mikepimez/FdD_Equipo_13/Fund Diseño/Talleres/Taller_10/Onshape Modelado 3D/README.md

# ONSHAPE Modelado 3D
## Link Ecovent:
## https://cad.onshape.com/documents/2ff0832ba7d75a162150be3a/w/7356b8713903647c55373f1b/e/d87a3bc96895a205dabae675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
