mikepimez/FdD_Equipo_13/Fund Diseño/Talleres/Taller_7/Certificados Onshape/Elmer David Bravo Tumbay/Introduction to onshape-Elmer David Bravo Tumbay.pdf

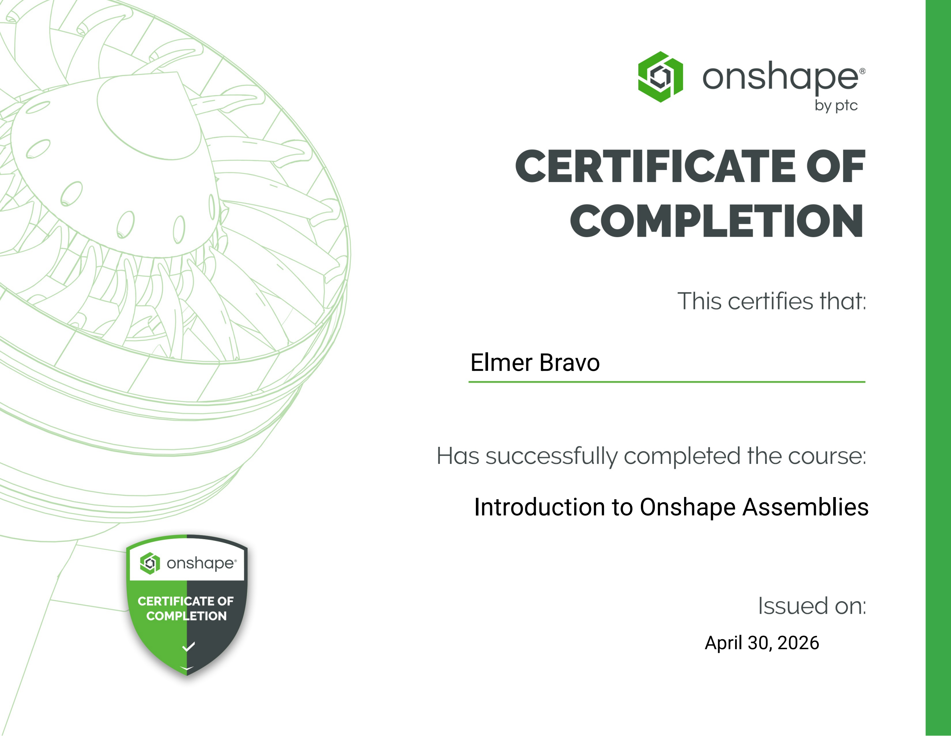
[picture p20: page 1]

Elmer Bravo

April 30, 2026

Introduction to Onshape Assemblies
