mikepimez/FdD_Equipo_13/Fund Diseño/Talleres/Taller_7/Certificados Onshape/Aldair Silvera Huaman/aldair-silvera-huaman-80f540d1-5e13-4ac5-9597-b1e16f2ed07b-certificate.pdf

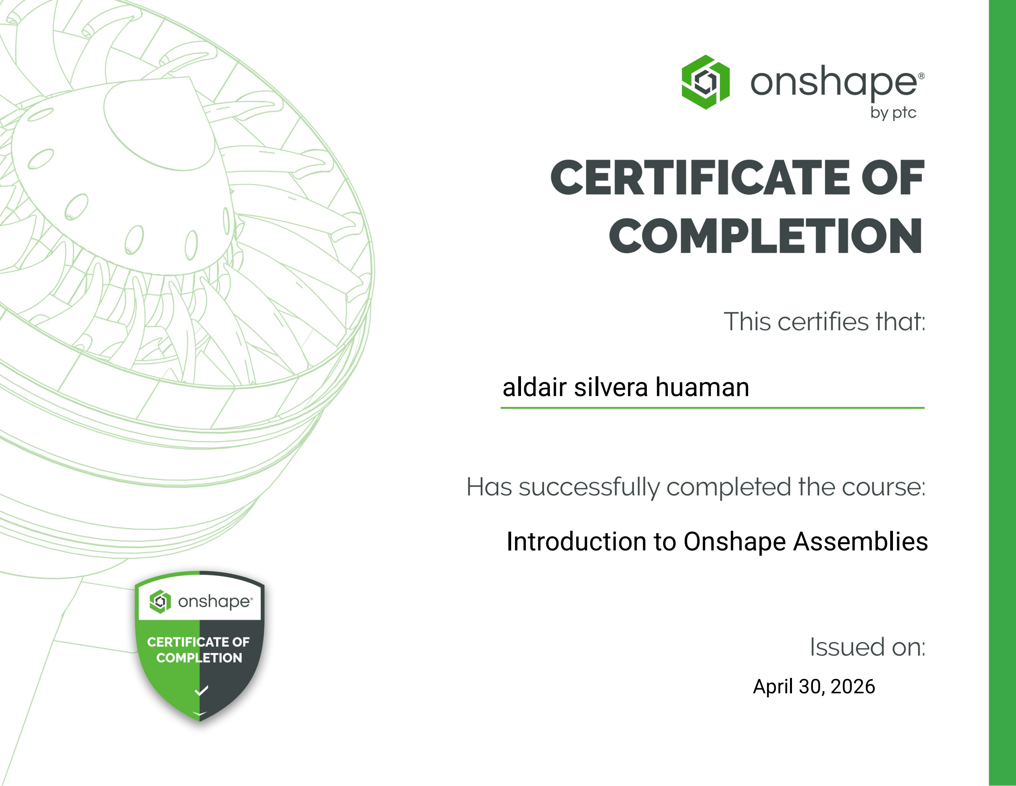
[picture p21: page 1]

aldair silvera huaman

April 30, 2026

Introduction to Onshape Assemblies
