mikepimez/FdD_Equipo_13/Fund Diseño/Talleres/Taller_7/Certificados Onshape/Milagros Lucero Romero Yllaconza/milagros-romero-127f4364-2a7c-48cf-9cd8-1c9b132f20d1-certificate.pdf

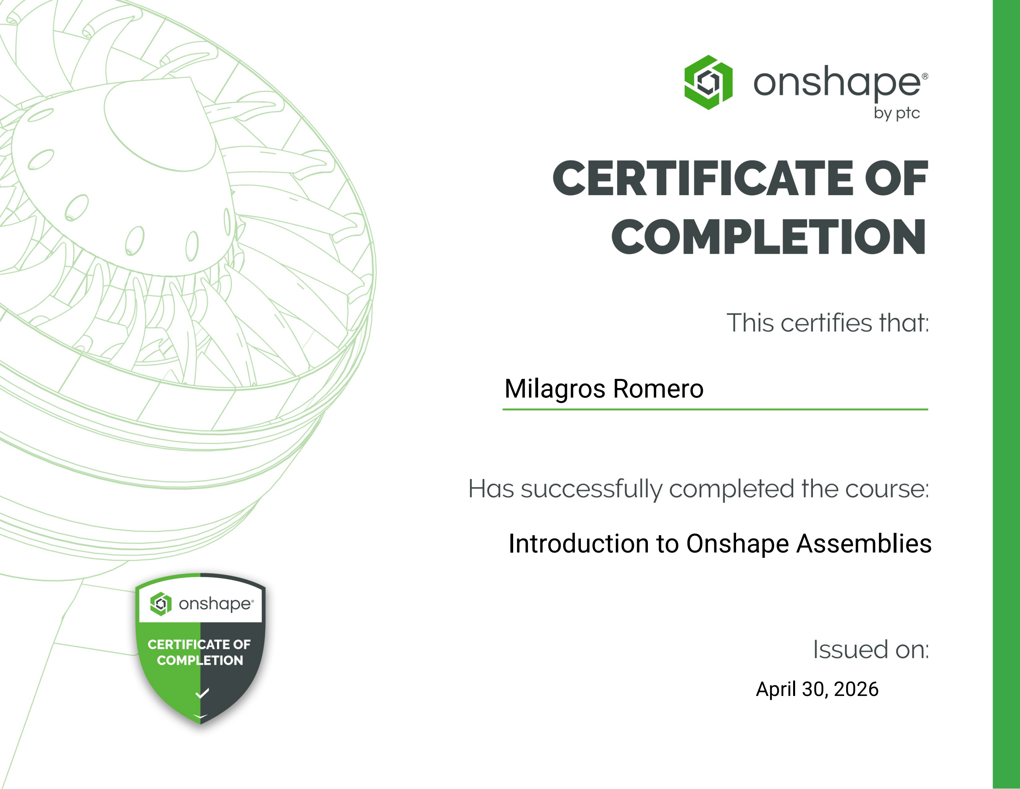
[picture p22: page 1]

Milagros Romero

April 30, 2026

Introduction to Onshape Assemblies
