mikepimez/FdD_Equipo_13/Proyecto/MóduloMecánico/Certificados/Milagros Romero Yllaconza/CertificadosUnidos.pdf

Milagros Romero

Introduction to Sketching

April 30, 2026

Milagros Romero

Introduction to Part Studios

April 30, 2026

Milagros Romero

April 30, 2026

Introduction to Onshape Assemblies

Milagros Romero

April 30, 2026

Detailed Drawings

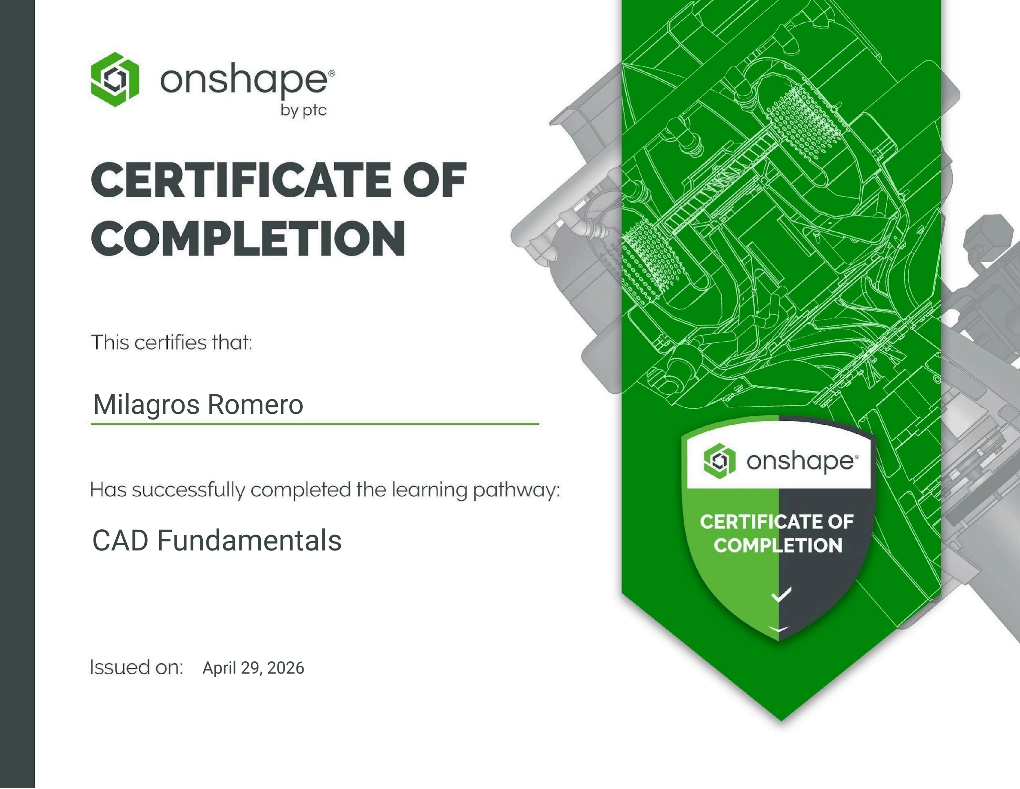
[picture p23: page 5]

Milagros Romero

CAD Fundamentals

April 29, 2026
