mikepimez/FdD_Equipo_13/Proyecto/MóduloMecánico/Certificados/Isabel Padilla Romero/CertificadosUnidos.pdf

Isabel Antonella Padilla Romero

Introduction to Sketching

April 30, 2026

Isabel Antonella Padilla Romero

Introduction to Part Studios

April 30, 2026

Isabel Antonella Padilla Romero

Introduction to Onshape Assemblies

April 30, 2026

Isabel Antonella Padilla Romero

Detailed Drawings

April 30, 2026

Isabel Antonella Padilla Romero

CAD Fundamentals

April 29, 2026
