mikepimez/FdD_Equipo_13/Proyecto/MóduloMecánico/Certificados/David Bravo Tumbay/CertificadosUnidos.pdf

Elmer Bravo

Introduction to Sketching

April 30, 2026

Elmer Bravo

Introduction to Part Studios

April 30, 2026

Elmer Bravo

April 30, 2026

Introduction to Onshape Assemblies

Elmer Bravo

April 30, 2026

Detailed Drawings

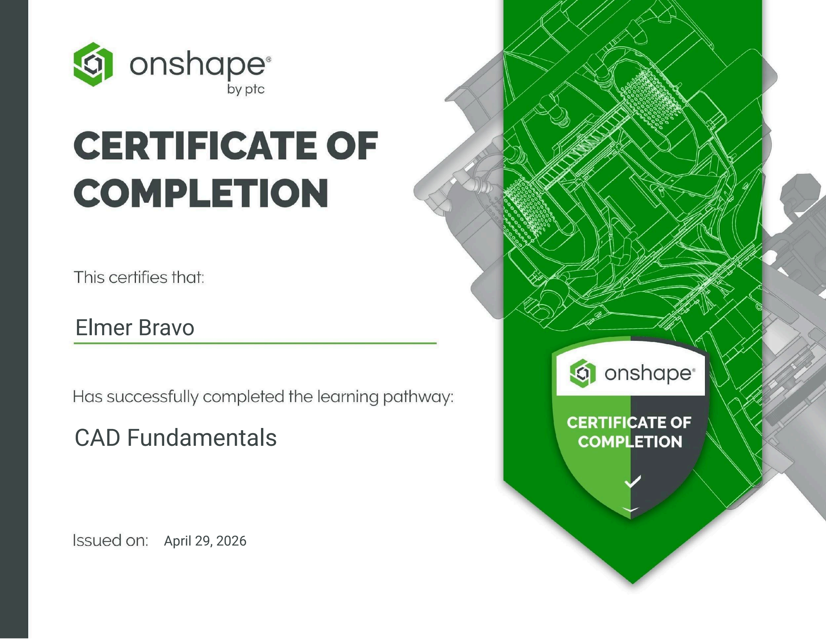
[picture p24: page 5]

Elmer Bravo

CAD Fundamentals

April 29, 2026
