mikepimez/FdD_Equipo_13/Proyecto/MóduloMecánico/Certificados/Aldair Silvera Huaman/CertificadosUnidos.pdf

aldair silvera huaman

Introduction to Sketching

April 30, 2026

aldair silvera huaman

Introduction to Part Studios

April 30, 2026

aldair silvera huaman

April 30, 2026

Introduction to Onshape Assemblies

aldair silvera huaman

April 30, 2026

Detailed Drawings

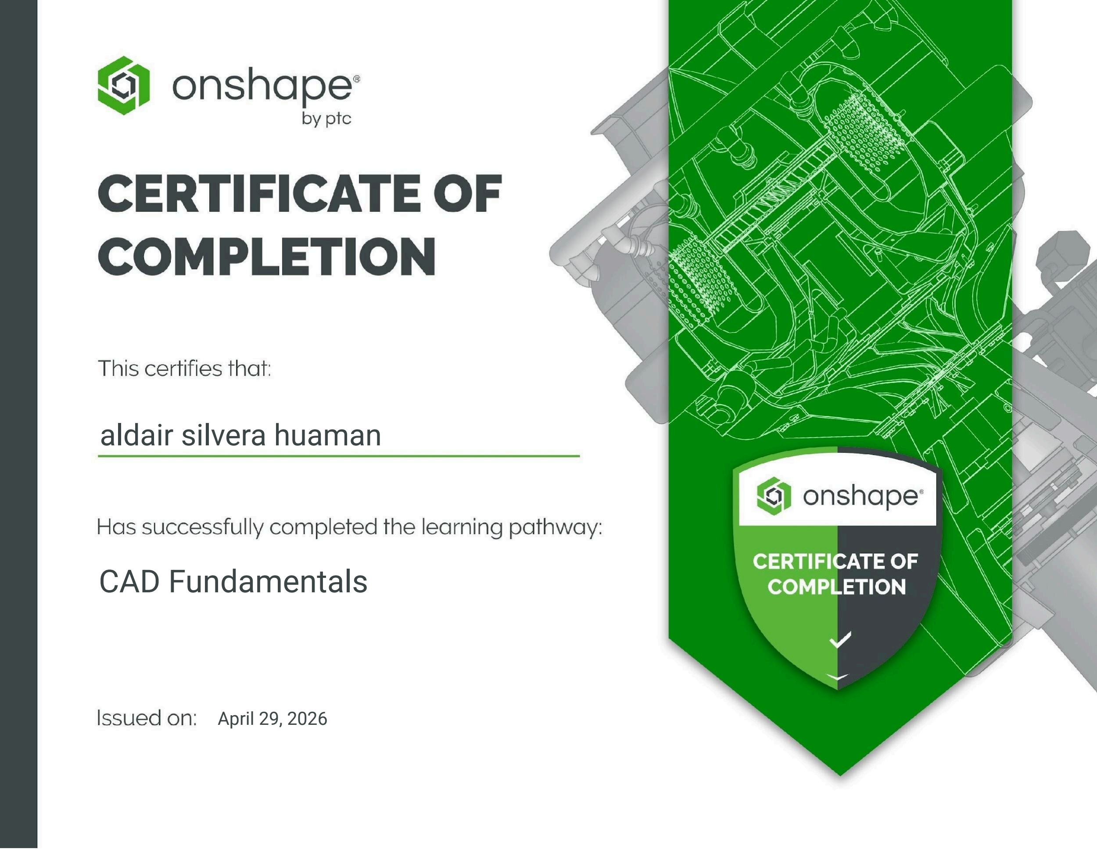
[picture p25: page 5]

aldair silvera huaman

CAD Fundamentals

April 29, 2026
