mikepimez/FdD_Equipo_13/Proyecto/MóduloMecánico/Certificados/Minoru Tapia Gómez/CertificadosUnidos.pdf

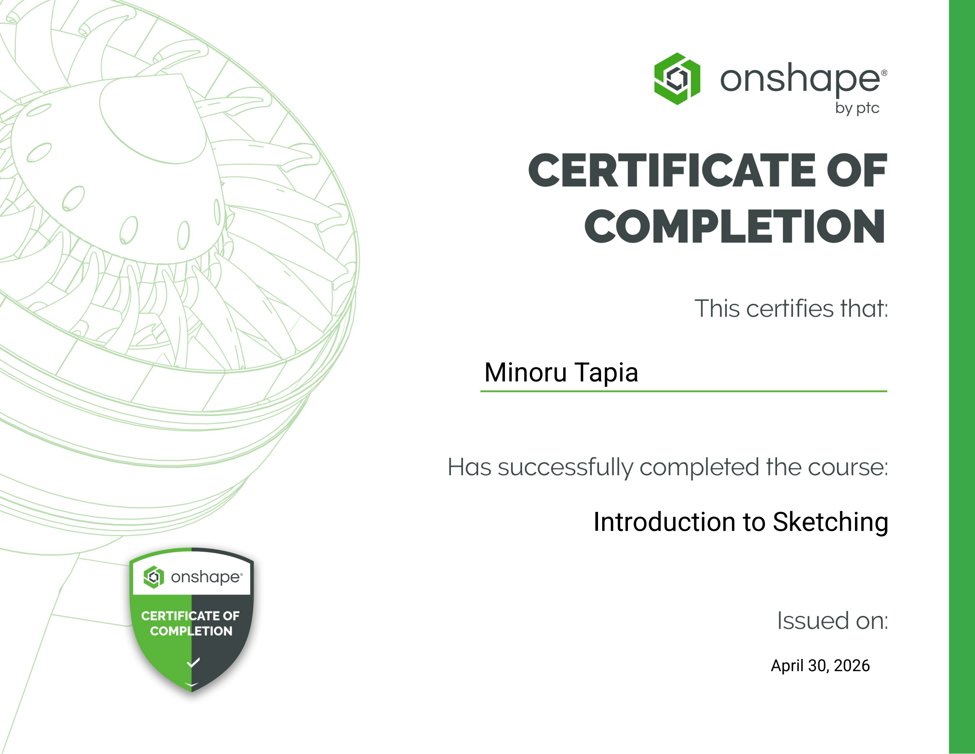
[picture p26: page 1]

## Minoru Tapia

## Introduction to Sketching

April 30, 2026

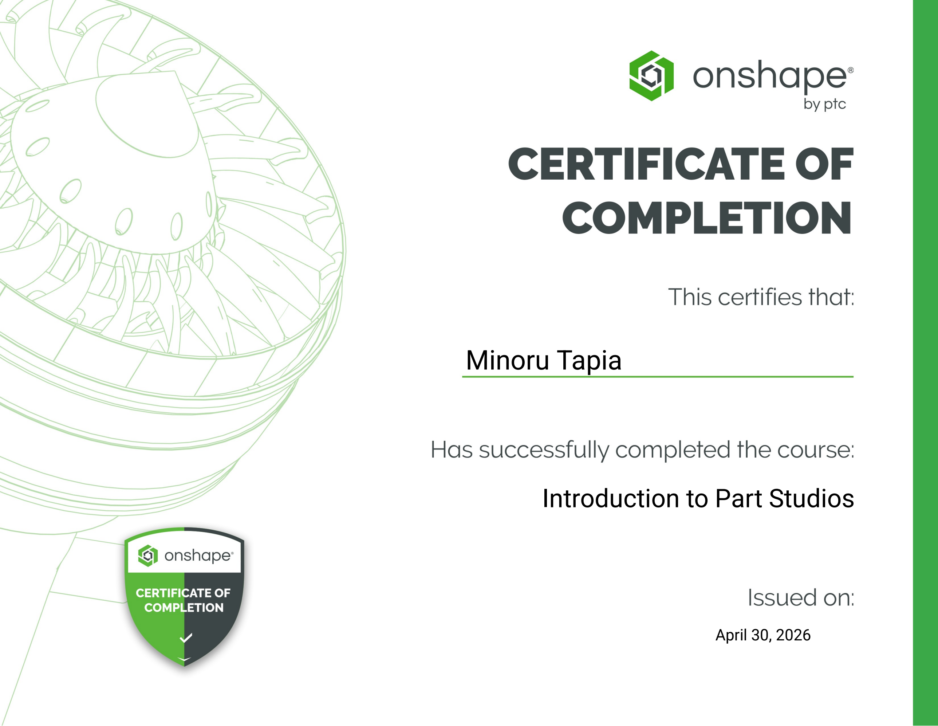
[picture p27: page 2]

## Minoru Tapia

## Introduction to Part Studios

April 30, 2026

Minoru Takeshi Tapia Gomez

Introduction to Onshape Assemblies

April 30, 2026

Minoru Takeshi Tapia Gomez

Detailed Drawings

April 30, 2026

Minoru Tapia

CAD Fundamentals

April 29, 2026
