mikepimez/FdD_Equipo_13/Fund Diseño/Talleres/Taller_7/Certificados Onshape/Elmer David Bravo Tumbay/Detaile Drawings-Elmer David Bravo Tumbay.pdf

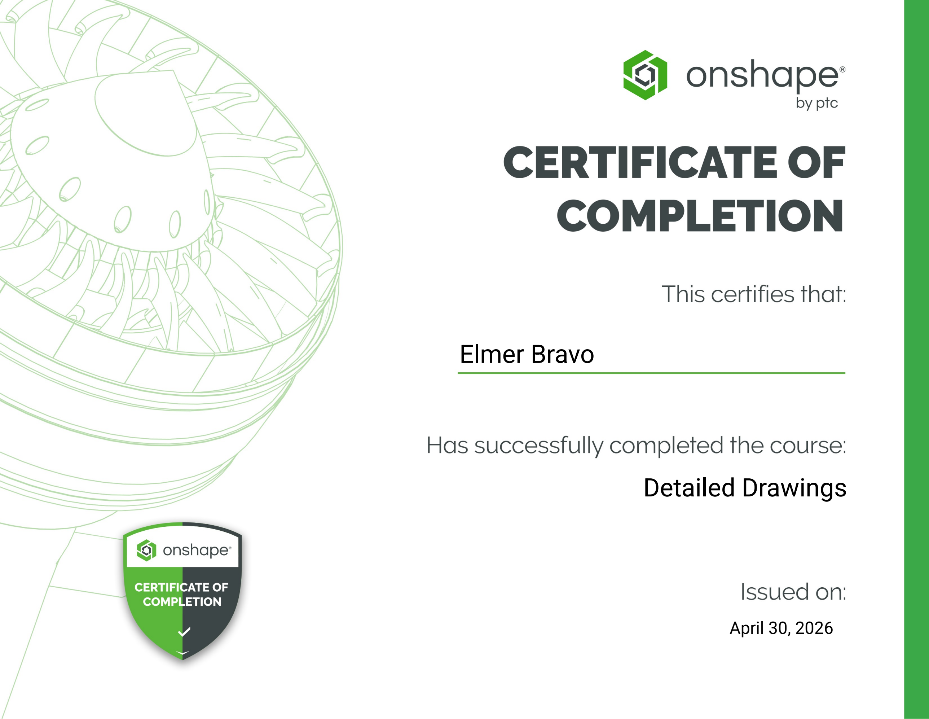
[picture p32: page 1]

Elmer Bravo

April 30, 2026

Detailed Drawings
