mikepimez/FdD_Equipo_13/Fund Diseño/Talleres/Taller_7/Certificados Onshape/Elmer David Bravo Tumbay/Introduction to part studios-Elmer David Bravo Tumbay.pdf

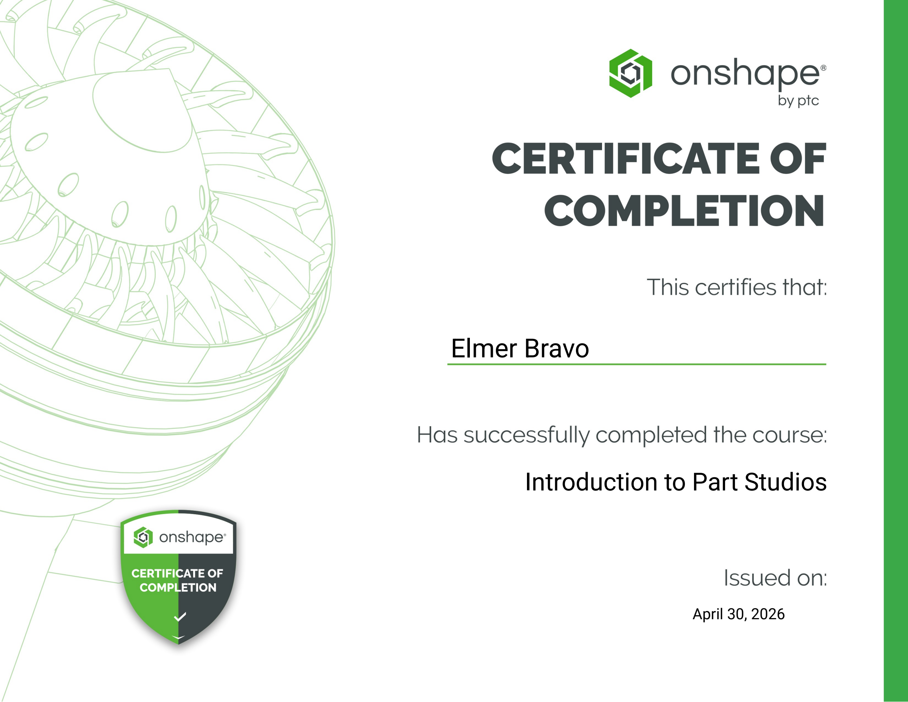
[picture p33: page 1]

Elmer Bravo

Introduction to Part Studios

April 30, 2026
