mikepimez/FdD_Equipo_13/Fund Diseño/Talleres/Taller_7/Certificados Onshape/Elmer David Bravo Tumbay/Introduction to sketching- Bravo Tumbay Elmer David.pdf

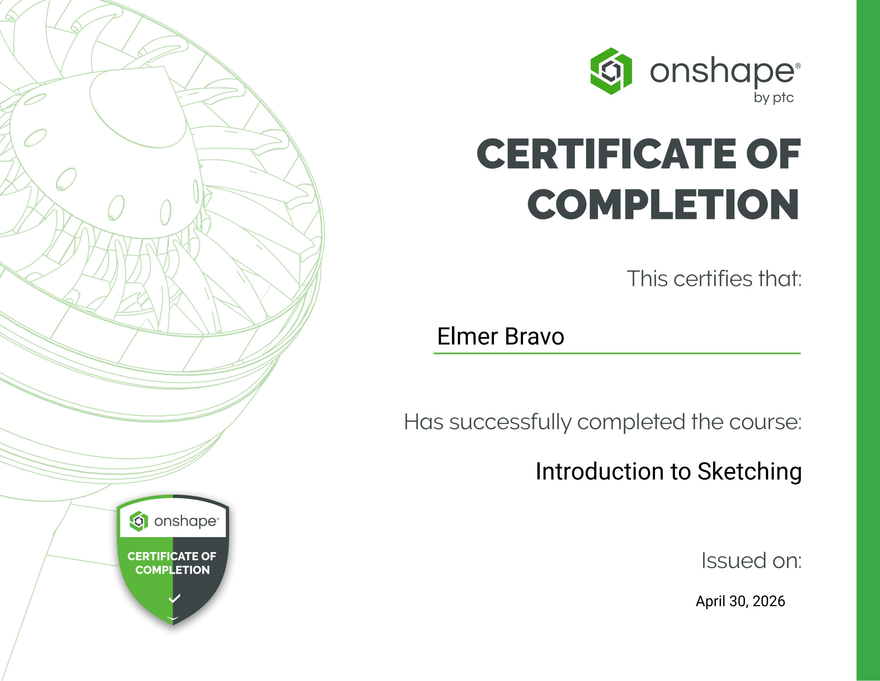
[picture p34: page 1]

Elmer Bravo

Introduction to Sketching

April 30, 2026
