mikepimez/FdD_Equipo_13/Fund Diseño/Talleres/Taller_7/Certificados Onshape/Aldair Silvera Huaman/aldair-silvera-huaman-4e8c6b65-7295-4350-af0d-eef3ffecdfa4-certificate.pdf

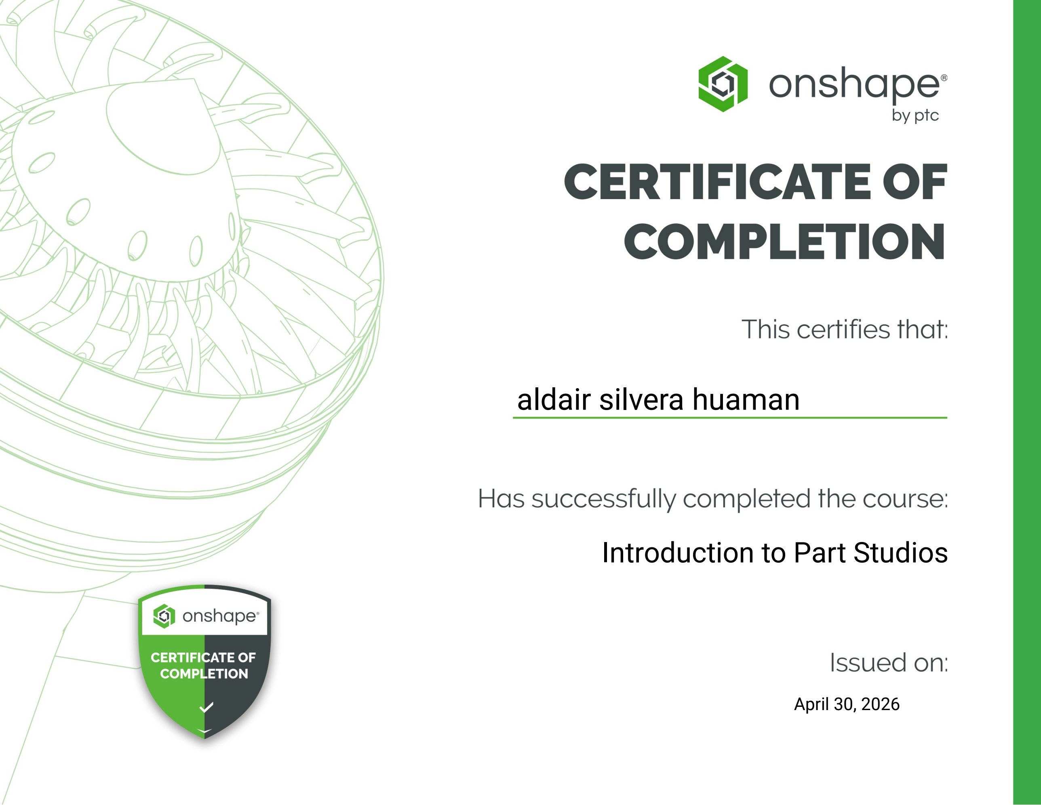
[picture p35: page 1]

aldair silvera huaman

Introduction to Part Studios

April 30, 2026
