mikepimez/FdD_Equipo_13/Fund Diseño/Talleres/Taller_7/Certificados Onshape/Aldair Silvera Huaman/aldair-silvera-huaman-e3dbeebc-8bc2-4efb-8675-0c4b83620323-certificate.pdf

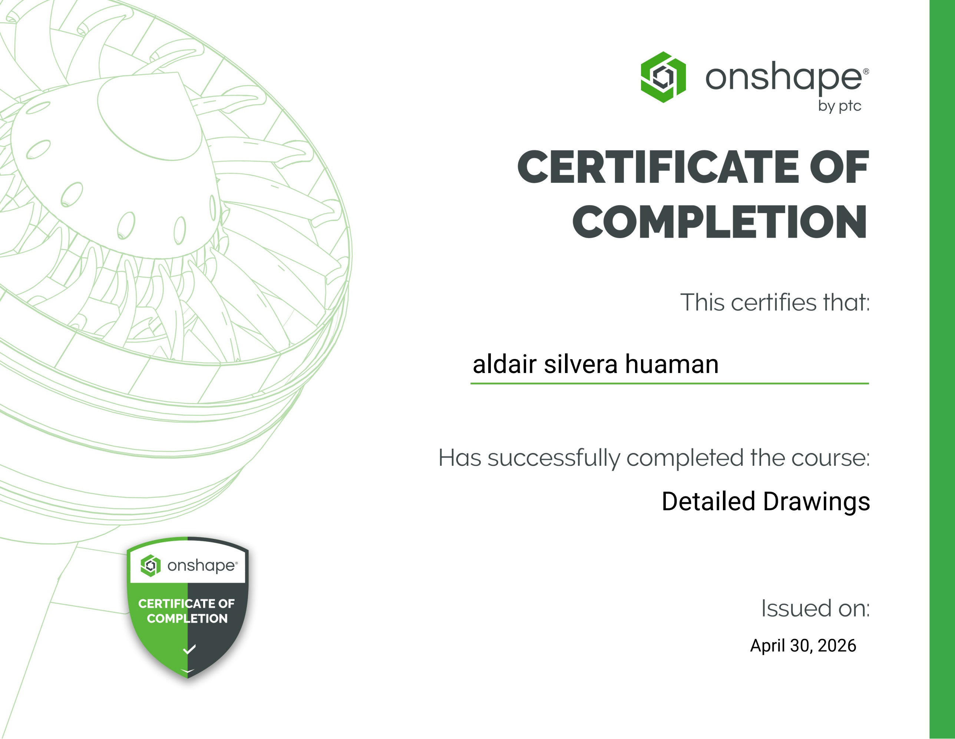
[picture p36: page 1]

aldair silvera huaman

April 30, 2026

Detailed Drawings
