mikepimez/FdD_Equipo_13/Fund Diseño/Talleres/Taller_7/Certificados Onshape/Aldair Silvera Huaman/aldair-silvera-huaman-eca4b5cf-689d-40fd-96bf-5592a26e97f9-certificate.pdf

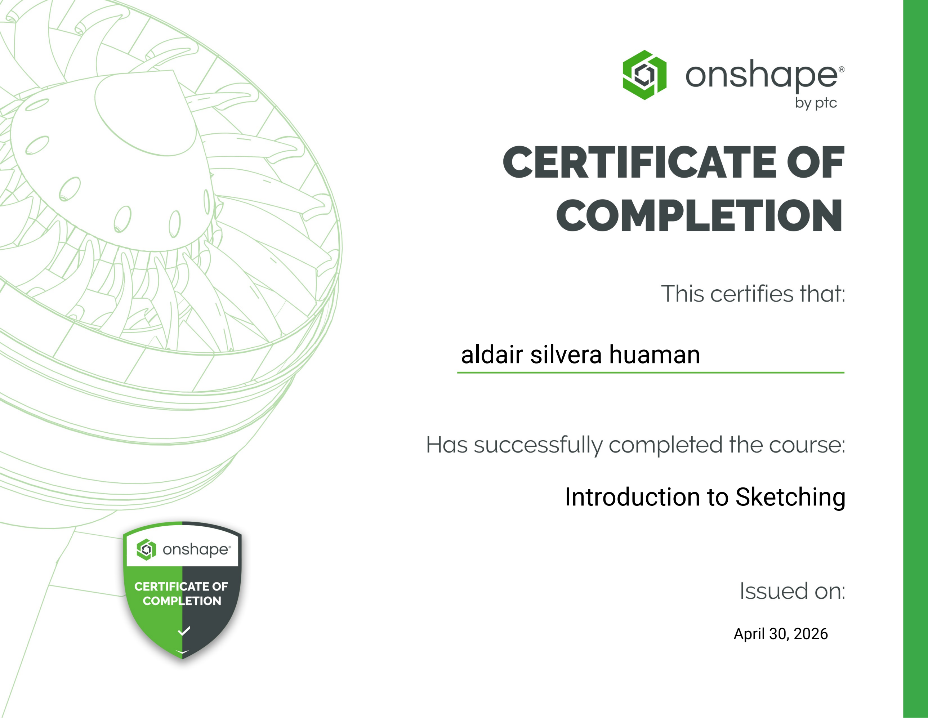
[picture p37: page 1]

aldair silvera huaman

Introduction to Sketching

April 30, 2026
