mikepimez/FdD_Equipo_13/Fund Diseño/Talleres/Taller_7/Certificados Onshape/Milagros Lucero Romero Yllaconza/milagros-romero-22843f85-eb03-4271-b142-8c62b271767d-certificate.pdf

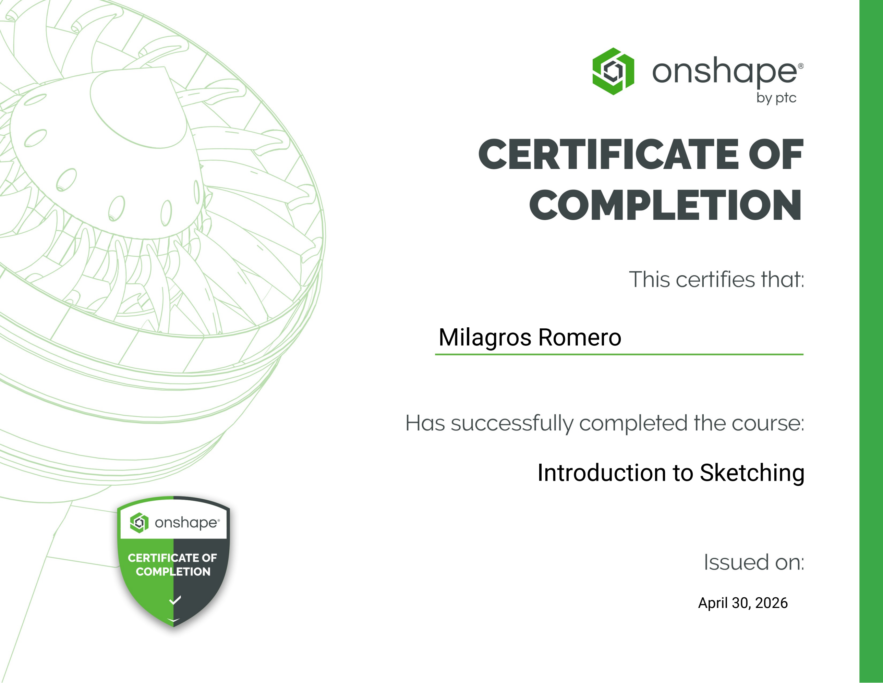
[picture p38: page 1]

Milagros Romero

Introduction to Sketching

April 30, 2026
