mikepimez/FdD_Equipo_13/Fund Diseño/Talleres/Taller_7/Certificados Onshape/Milagros Lucero Romero Yllaconza/milagros-romero-844ef38e-39e2-414a-8ad2-bcf23b460bee-certificate.pdf

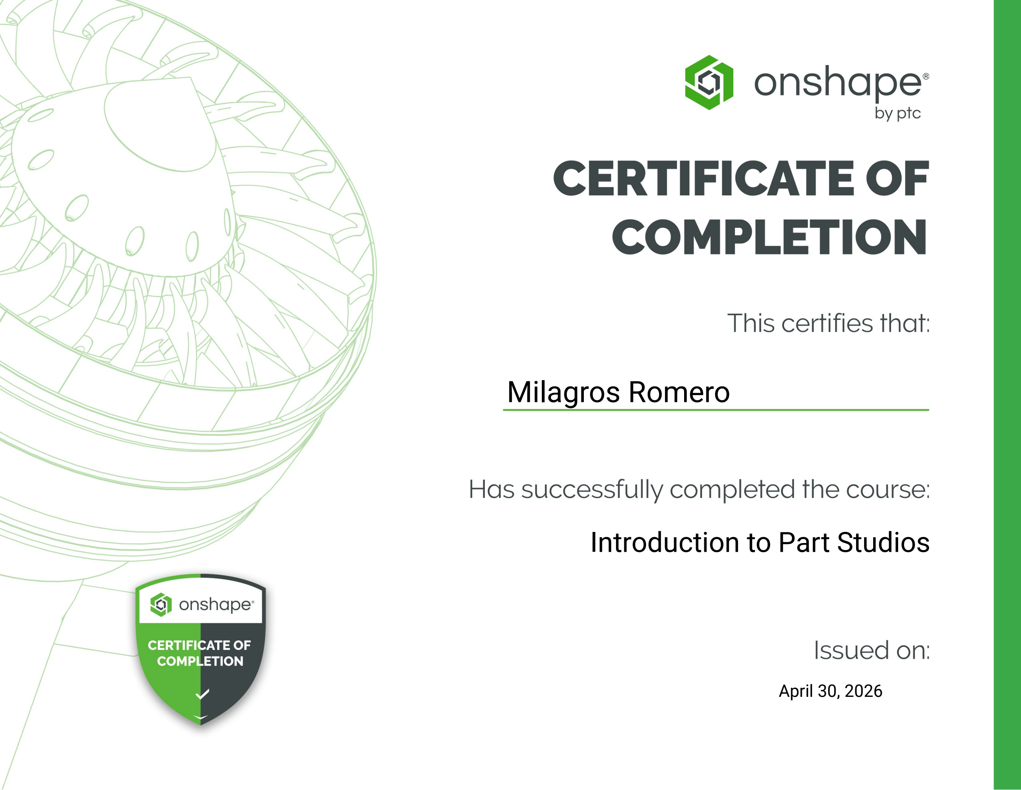
[picture p39: page 1]

Milagros Romero

Introduction to Part Studios

April 30, 2026
