mikepimez/FdD_Equipo_13/Fund Diseño/Talleres/Taller_7/Certificados Onshape/Milagros Lucero Romero Yllaconza/milagros-romero-93da2aa8-beca-4e25-bb0d-afc975d9d456-certificate.pdf

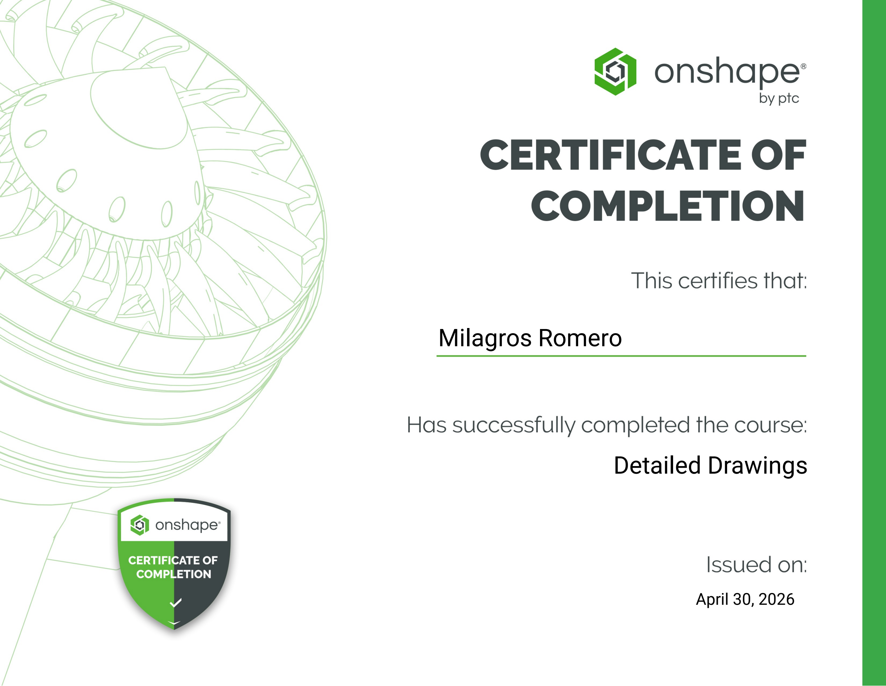
[picture p40: page 1]

Milagros Romero

April 30, 2026

Detailed Drawings
