mikepimez/FdD_Equipo_13/Fund Diseño/Talleres/Taller_7/Certificados Onshape/Isabel Antonella Padilla Romero/Introduction to Part Studios - Isabel Antonella Padilla Romero.pdf

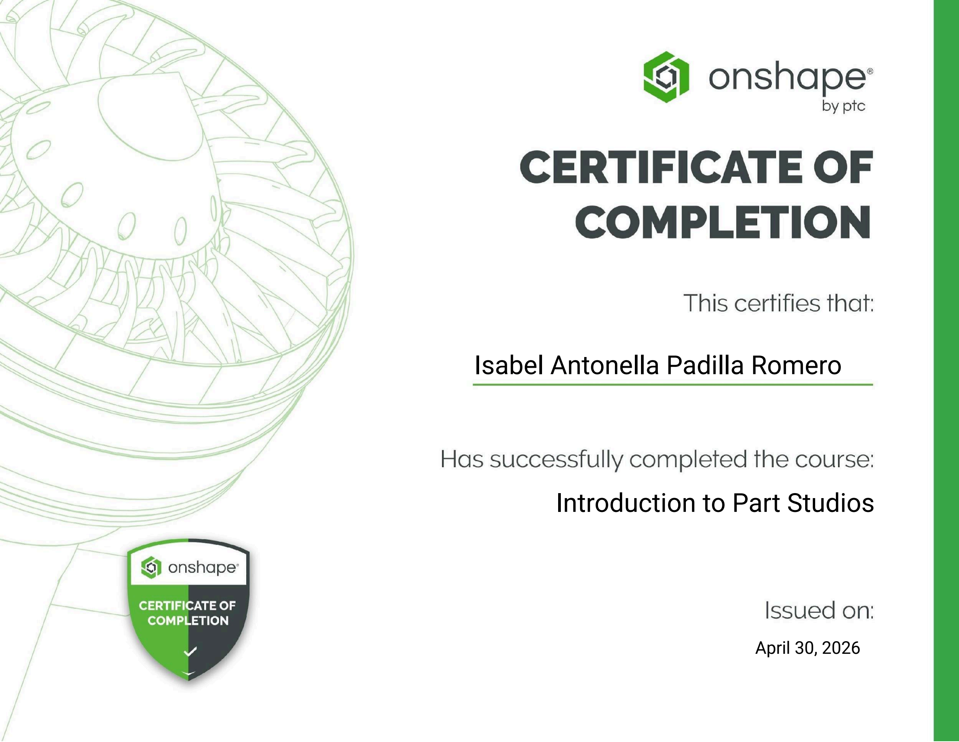
[picture p41: page 1]

Isabel Antonella Padilla Romero

Introduction to Part Studios

April 30, 2026
