mikepimez/FdD_Equipo_13/Fund Diseño/Talleres/Taller_7/Certificados Onshape/Isabel Antonella Padilla Romero/Introduction to Sketching - Isabel Antonella Padilla Romero.pdf

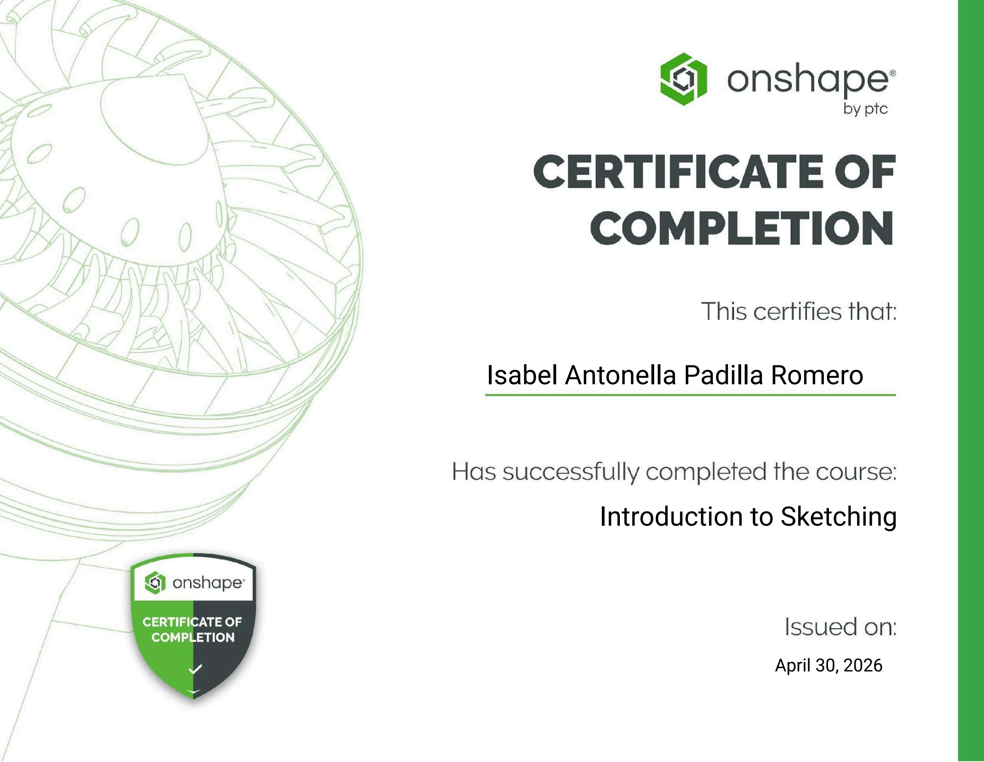
[picture p42: page 1]

Isabel Antonella Padilla Romero

Introduction to Sketching

April 30, 2026
