mikepimez/FdD_Equipo_13/Fund Diseño/Talleres/Taller_7/Certificados Onshape/Minoru Takeshi Tapia Gómez/Introduction to Sketching - Minoru Tapia Gomez.pdf

Minoru Tapia

Introduction to Sketching

April 30, 2026
