mikepimez/FdD_Equipo_13/Fund Diseño/Talleres/Taller_7/Certificados Onshape/Minoru Takeshi Tapia Gómez/Introduction to Part Estudios - Minoru Tapia Gomez.pdf

Minoru Tapia

Introduction to Part Studios

April 30, 2026
