mikepimez/FdD_Equipo_13/Fund Diseño/Talleres/Taller_7/Certificados Onshape/Minoru Takeshi Tapia Gómez/Detailed Drawings - Minoru Takeshi Tapia Gomez.pdf

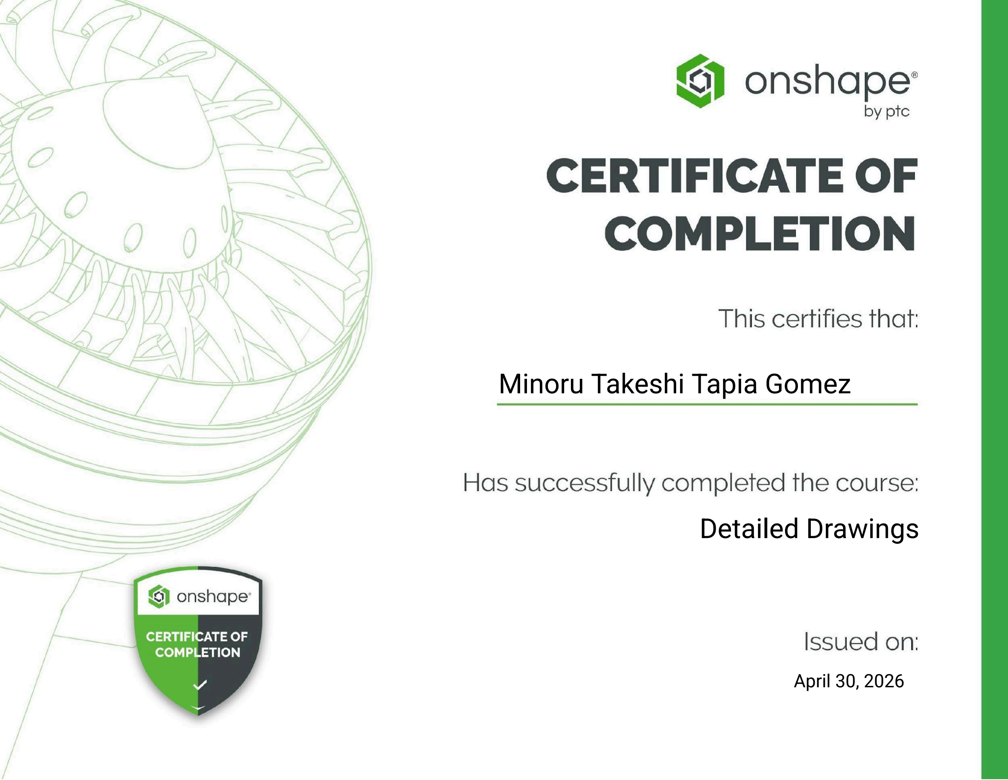
[picture p43: page 1]

Minoru Takeshi Tapia Gomez

Detailed Drawings

April 30, 2026
