mikepimez/FdD_Equipo_13/Fund Diseño/Talleres/Taller_7/Certificados Onshape/Isabel Antonella Padilla Romero/Detailed Drawings - Isabel Antonella Padilla Romero.pdf

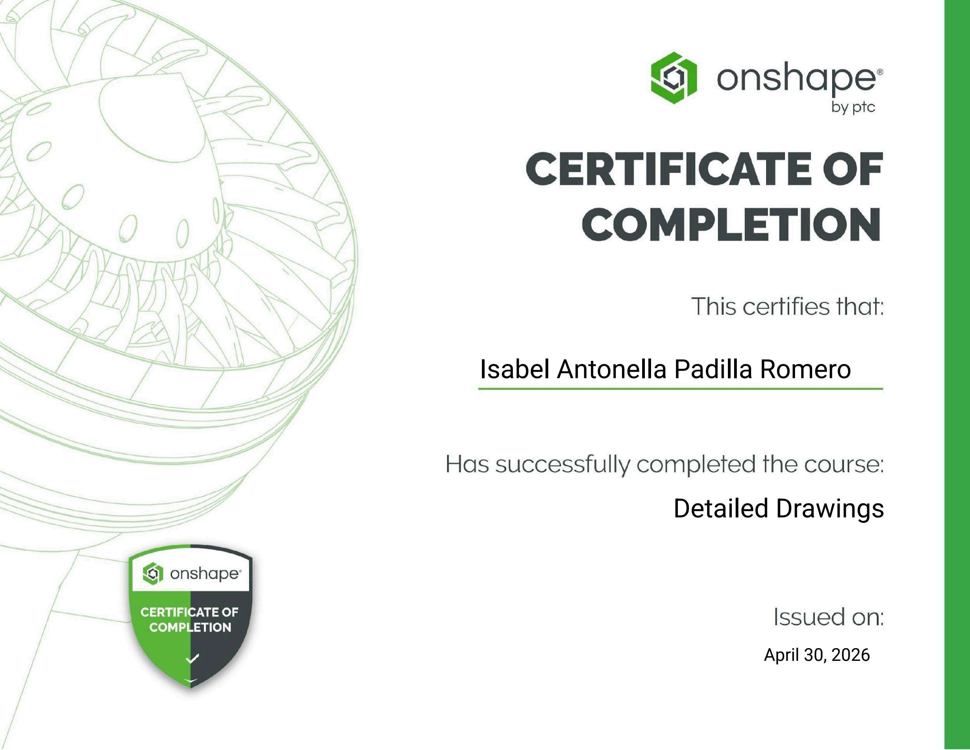
[picture p44: page 1]

Isabel Antonella Padilla Romero

Detailed Drawings

April 30, 2026
