mikepimez/FdD_Equipo_13/Proyecto/MóduloMecánico/VFINAL/Bocetos/Boceto interior VFINAL.pdf

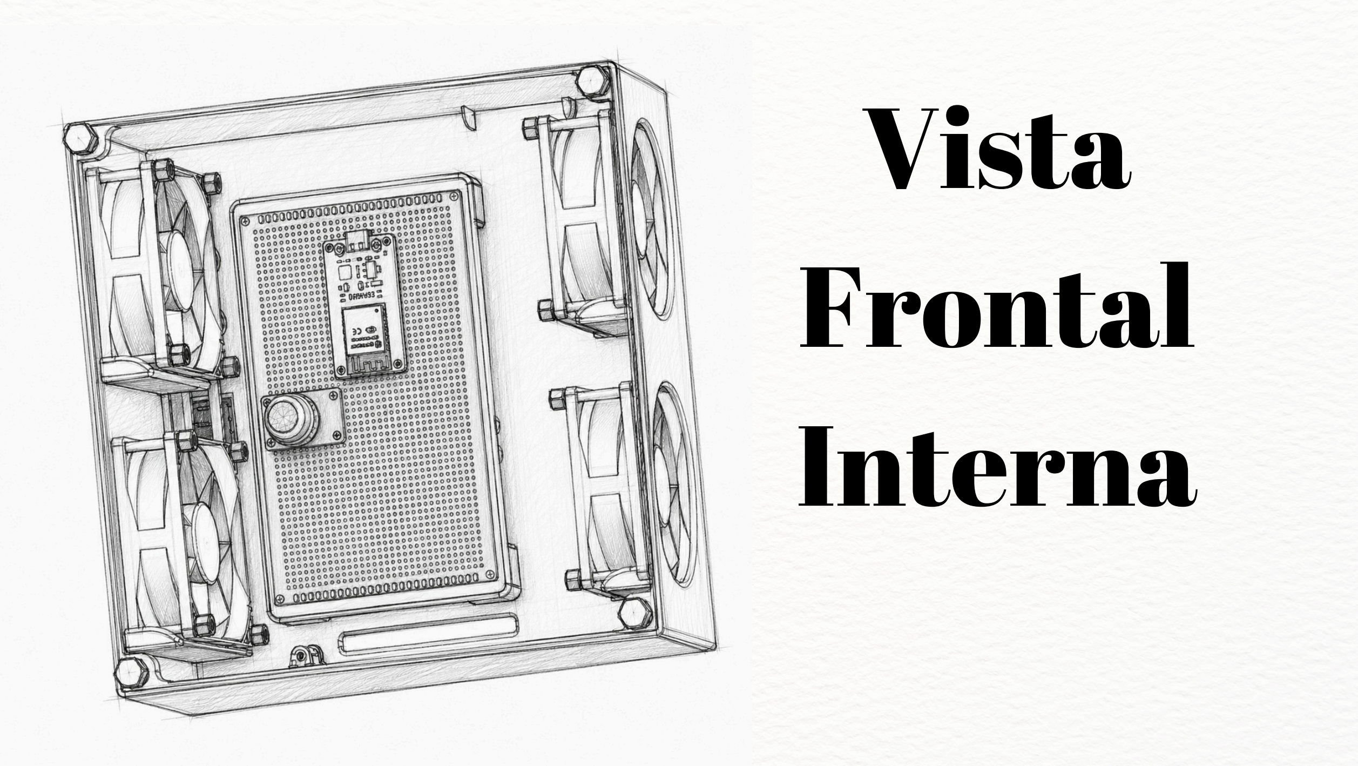
[picture p45: page 1]

Vista
Frontal
Interna
