mikepimez/FdD_Equipo_13/Fund Diseño/Talleres/Taller_10/Certificados/Advanced Onshape Assemblies - Aldair Silvera Huaman.pdf

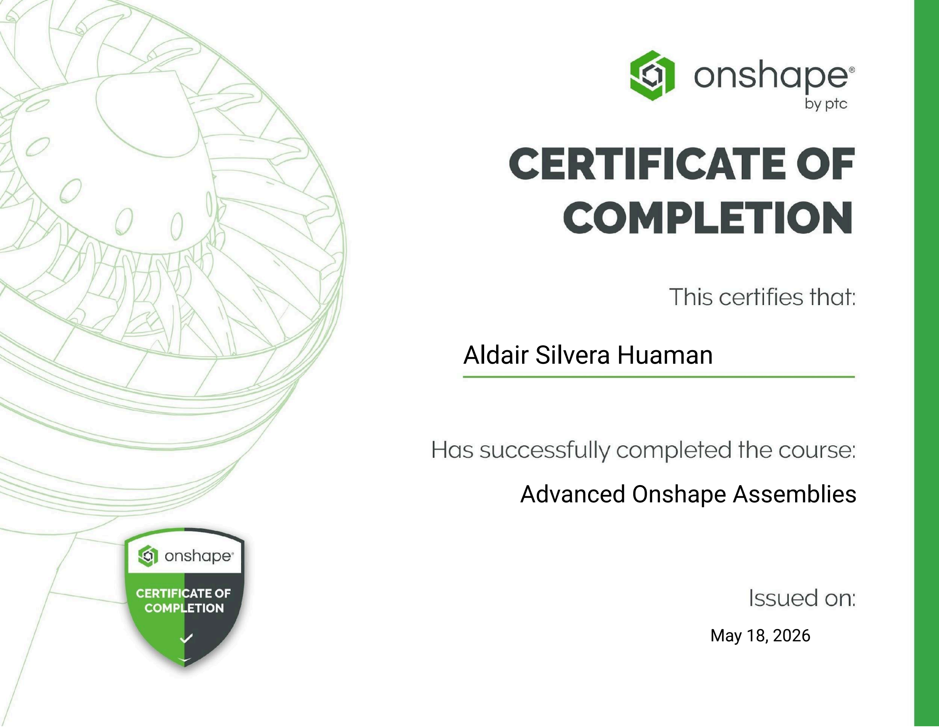
[picture p62: page 1]

Aldair Silvera Huaman

Advanced Onshape Assemblies

May 18, 2026
