mikepimez/FdD_Equipo_13/Fund Diseño/Talleres/Taller_10/Certificados/Advanced Onshape Assemblies - Elmer David Bravo Tumbay.pdf

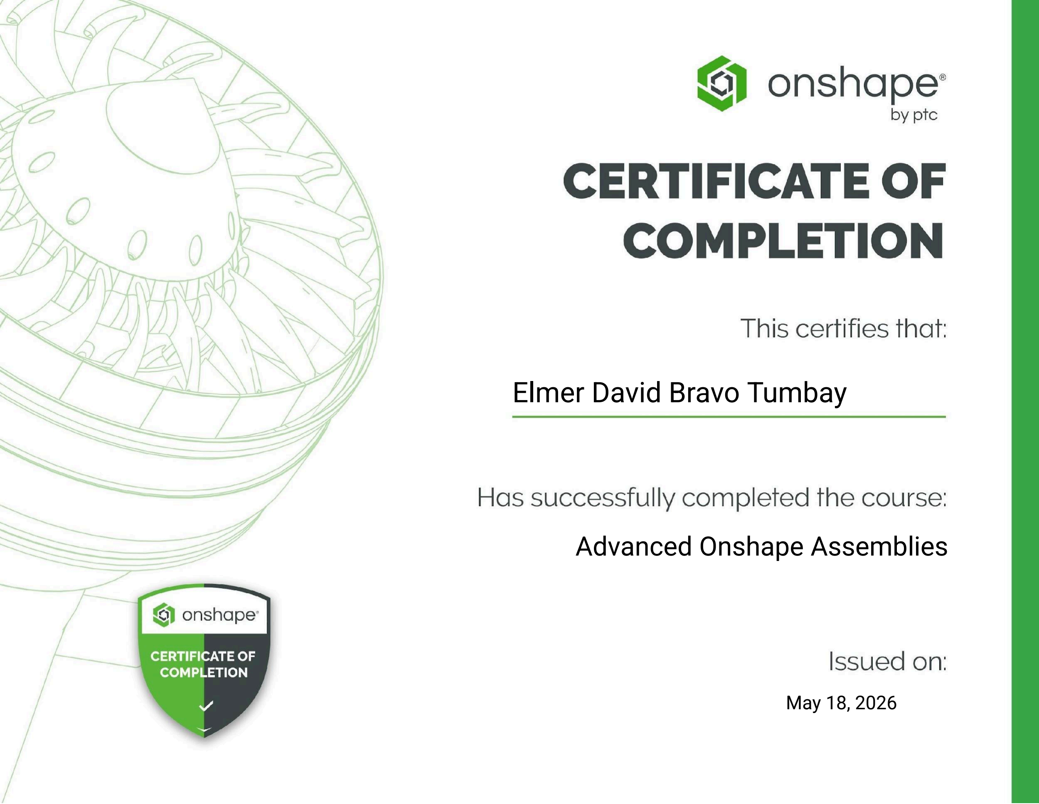
[picture p63: page 1]

Elmer David Bravo Tumbay

Advanced Onshape Assemblies

May 18, 2026
