mikepimez/FdD_Equipo_13/Fund Diseño/Talleres/Taller_10/Certificados/Advanced Onshape Assemblies - Isabel Antonella Padilla Romero.pdf

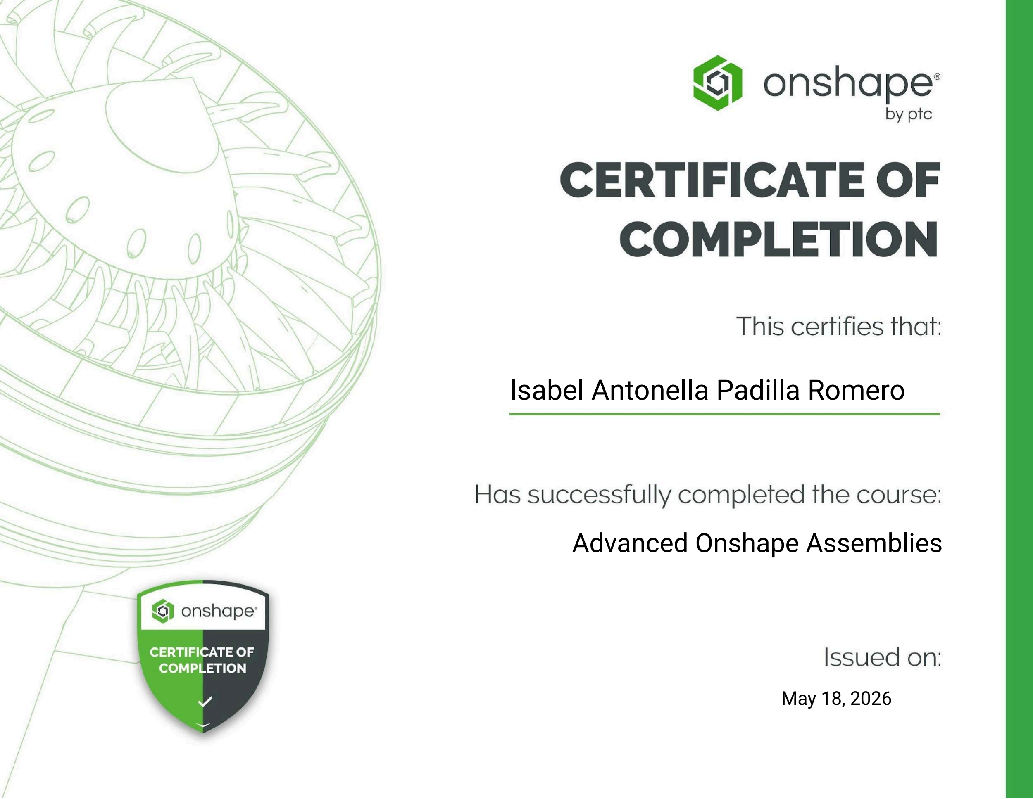
[picture p64: page 1]

Isabel Antonella Padilla Romero

Advanced Onshape Assemblies

May 18, 2026
