mikepimez/FdD_Equipo_13/Fund Diseño/Talleres/Taller_10/Certificados/Advanced Onshape Assemblies - Milagros Lucero Romero Yllaconza.pdf

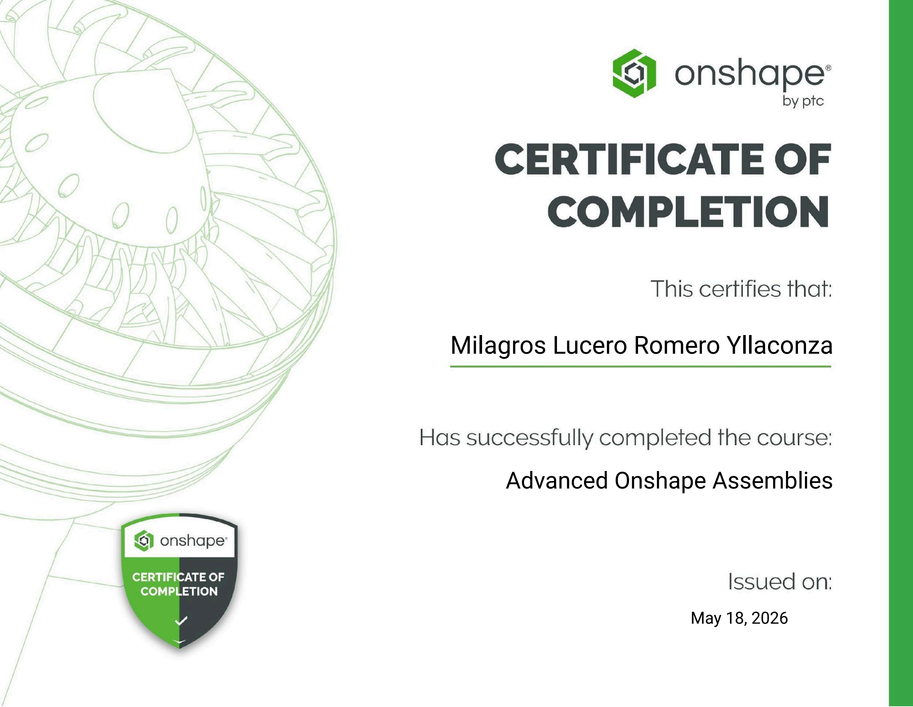
[picture p65: page 1]

Milagros Lucero Romero Yllaconza

Advanced Onshape Assemblies

May 18, 2026
