mikepimez/FdD_Equipo_13/Fund Diseño/Talleres/Taller_10/Certificados/Advanced Onshape Assemblies - Minoru Takeshi Tapia Gomez.pdf

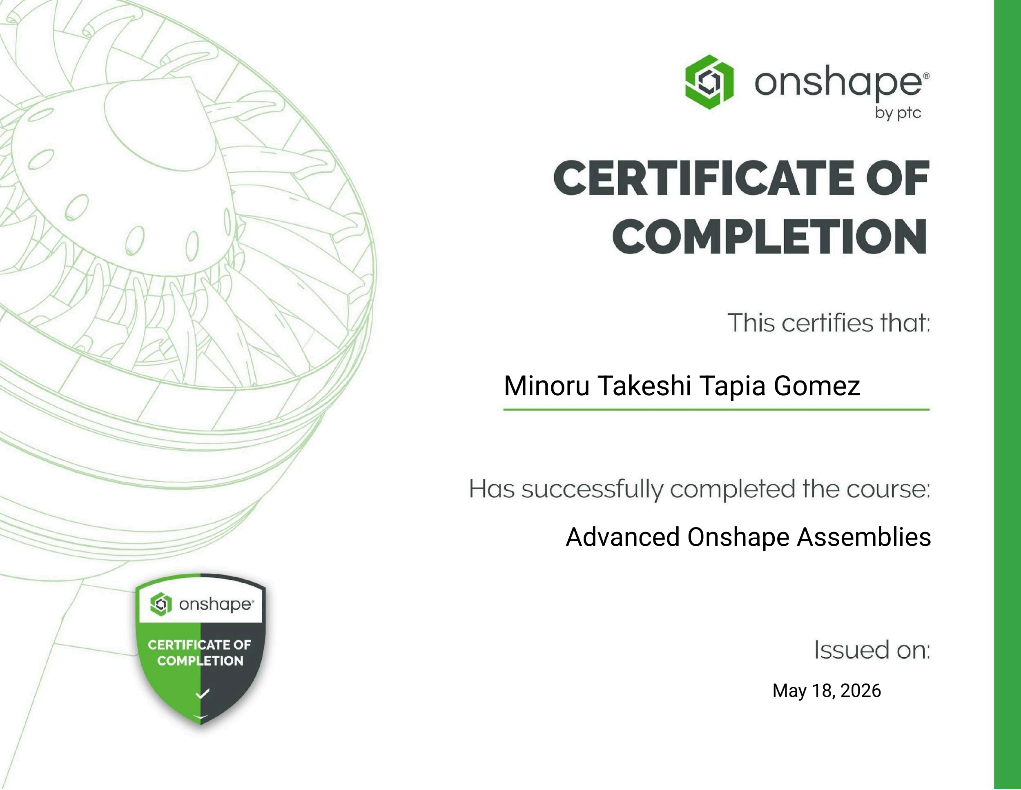
[picture p66: page 1]

Minoru Takeshi Tapia Gomez

Advanced Onshape Assemblies

May 18, 2026
