mikepimez/FdD_Equipo_13/Fund Diseño/Talleres/Taller_7/Certificados Onshape/Isabel Antonella Padilla Romero/Introduction to Onshape Assemblies - Isabel Antonella Padilla Romero.pdf

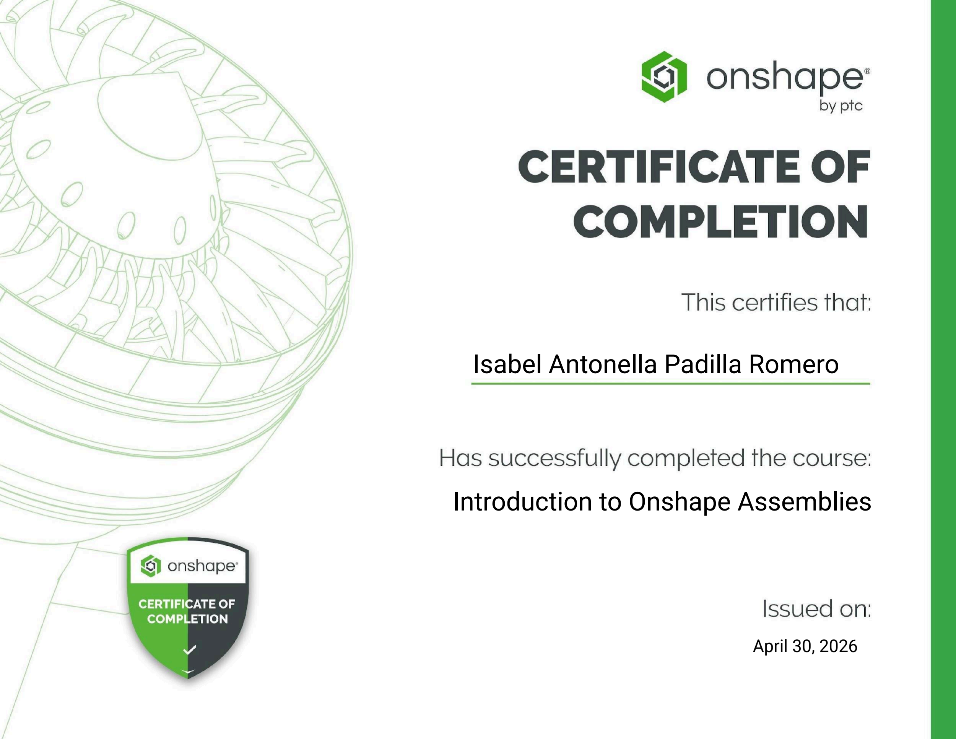
[picture p67: page 1]

Isabel Antonella Padilla Romero

Introduction to Onshape Assemblies

April 30, 2026
