mikepimez/FdD_Equipo_13/Fund Diseño/Talleres/Taller_7/Certificados Onshape/Minoru Takeshi Tapia Gómez/Introduction to Onshape Assemblies - Minoru Takeshi Tapia Gomez.pdf

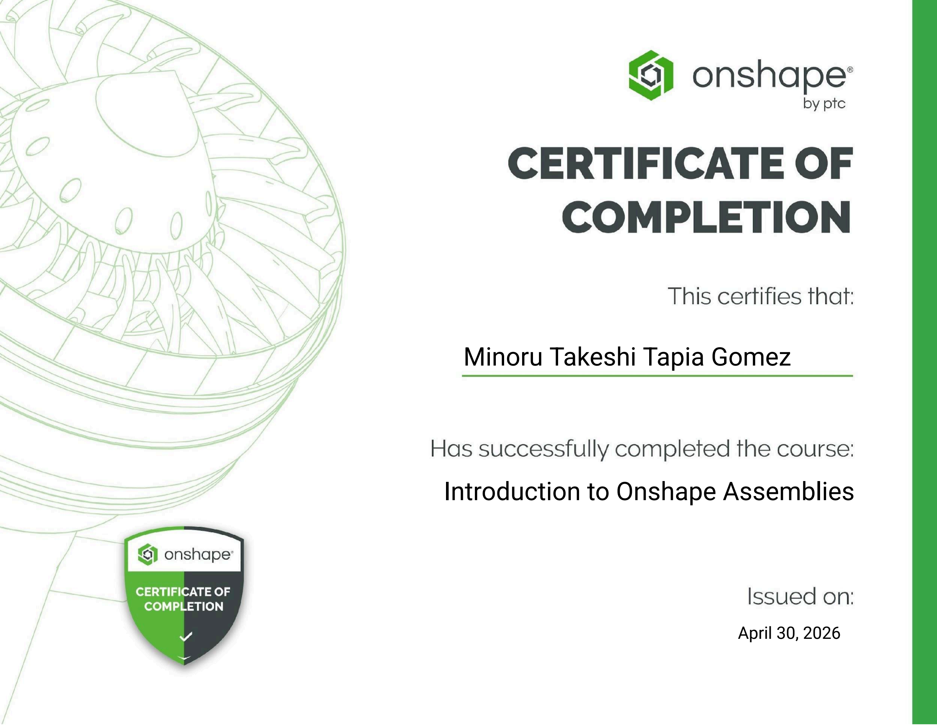
[picture p68: page 1]

Minoru Takeshi Tapia Gomez

Introduction to Onshape Assemblies

April 30, 2026
