mikepimez/FdD_Equipo_13/Proyecto/MóduloMecánico/VFINAL/Onshape/Planos/ECOVENT Caja Base.pdf

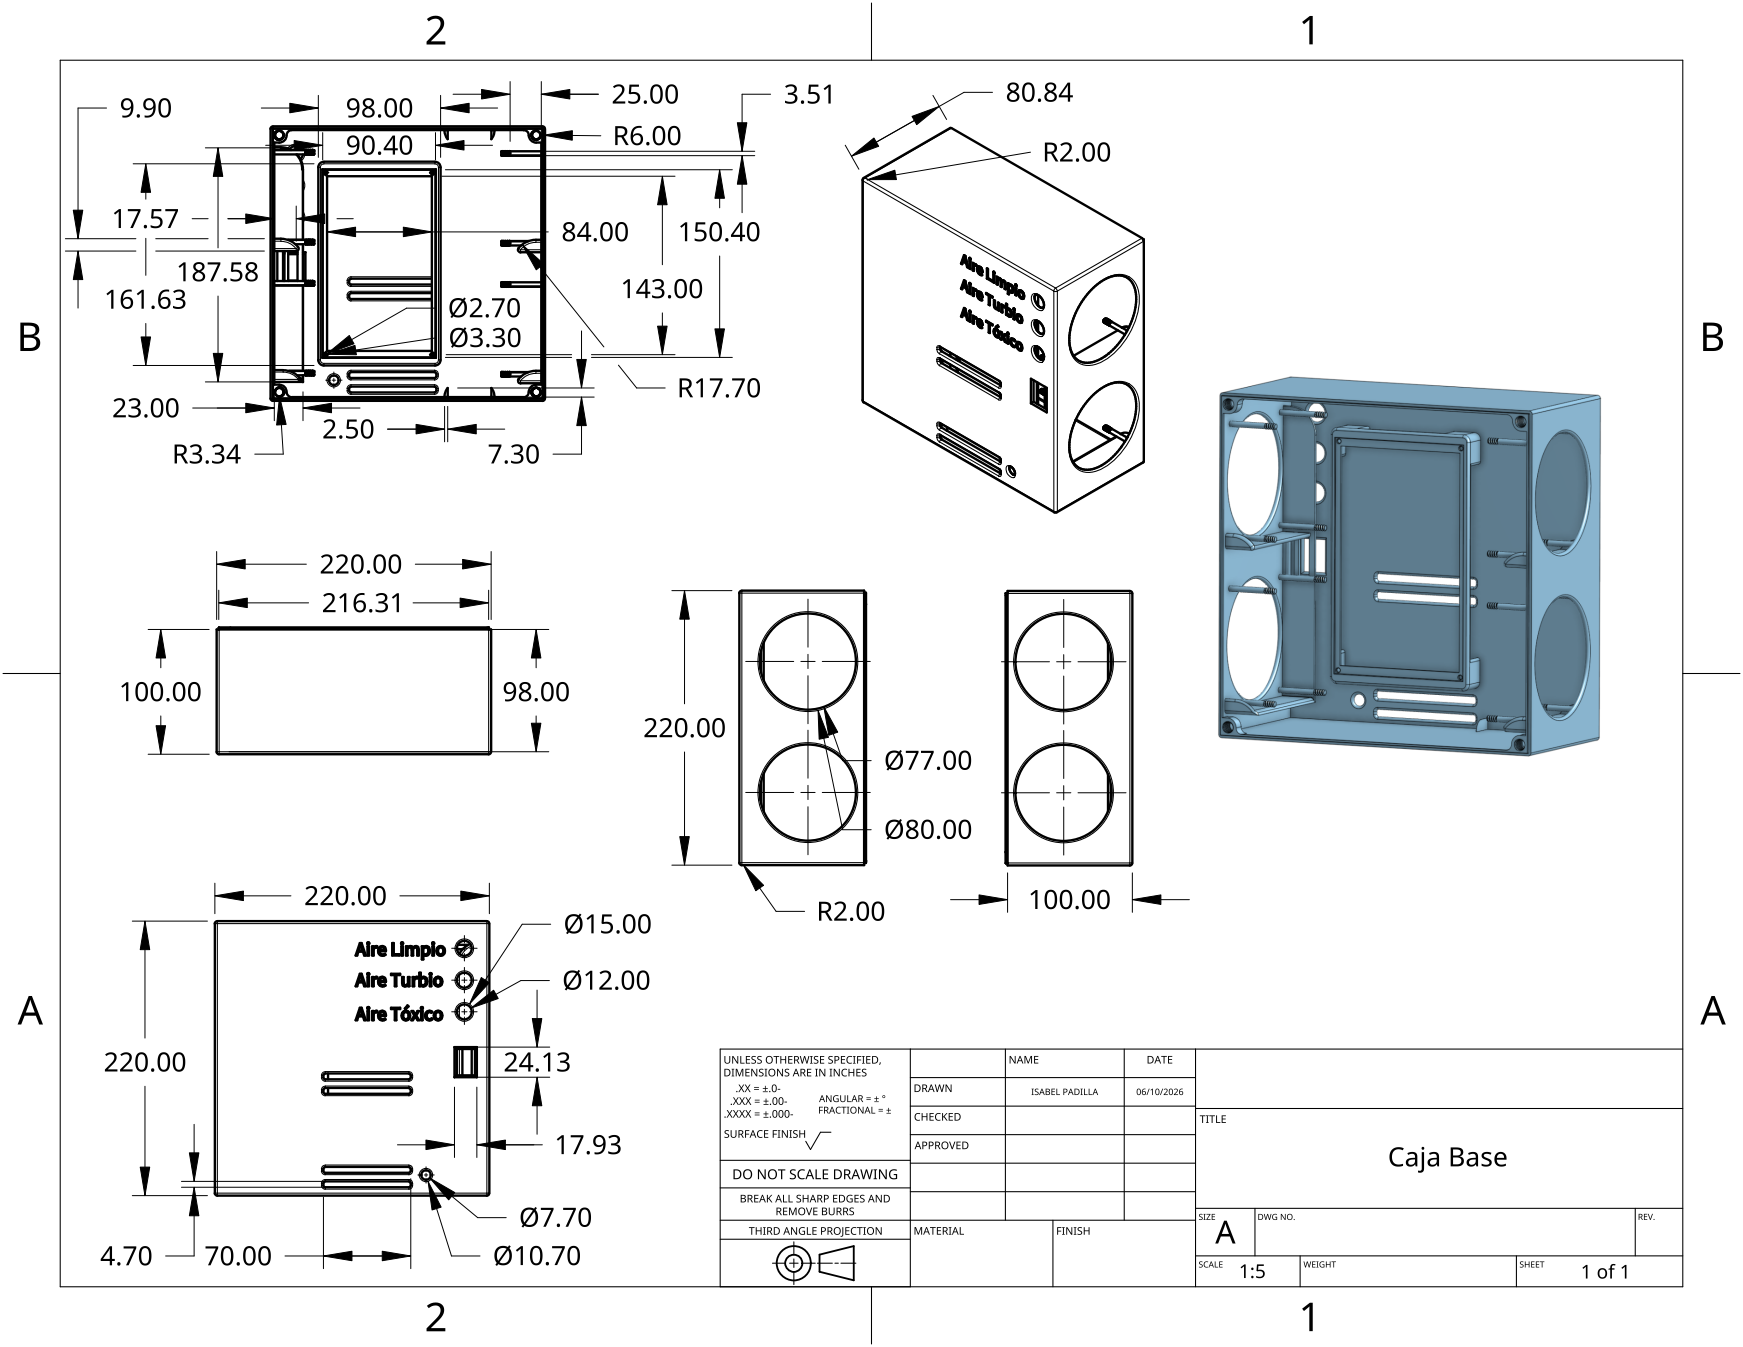
[picture p75: page 1]
