mikepimez/FdD_Equipo_13/Proyecto/MóduloMecánico/VFINAL/Onshape/Planos/ECOVENT Tapa de la Caja.pdf

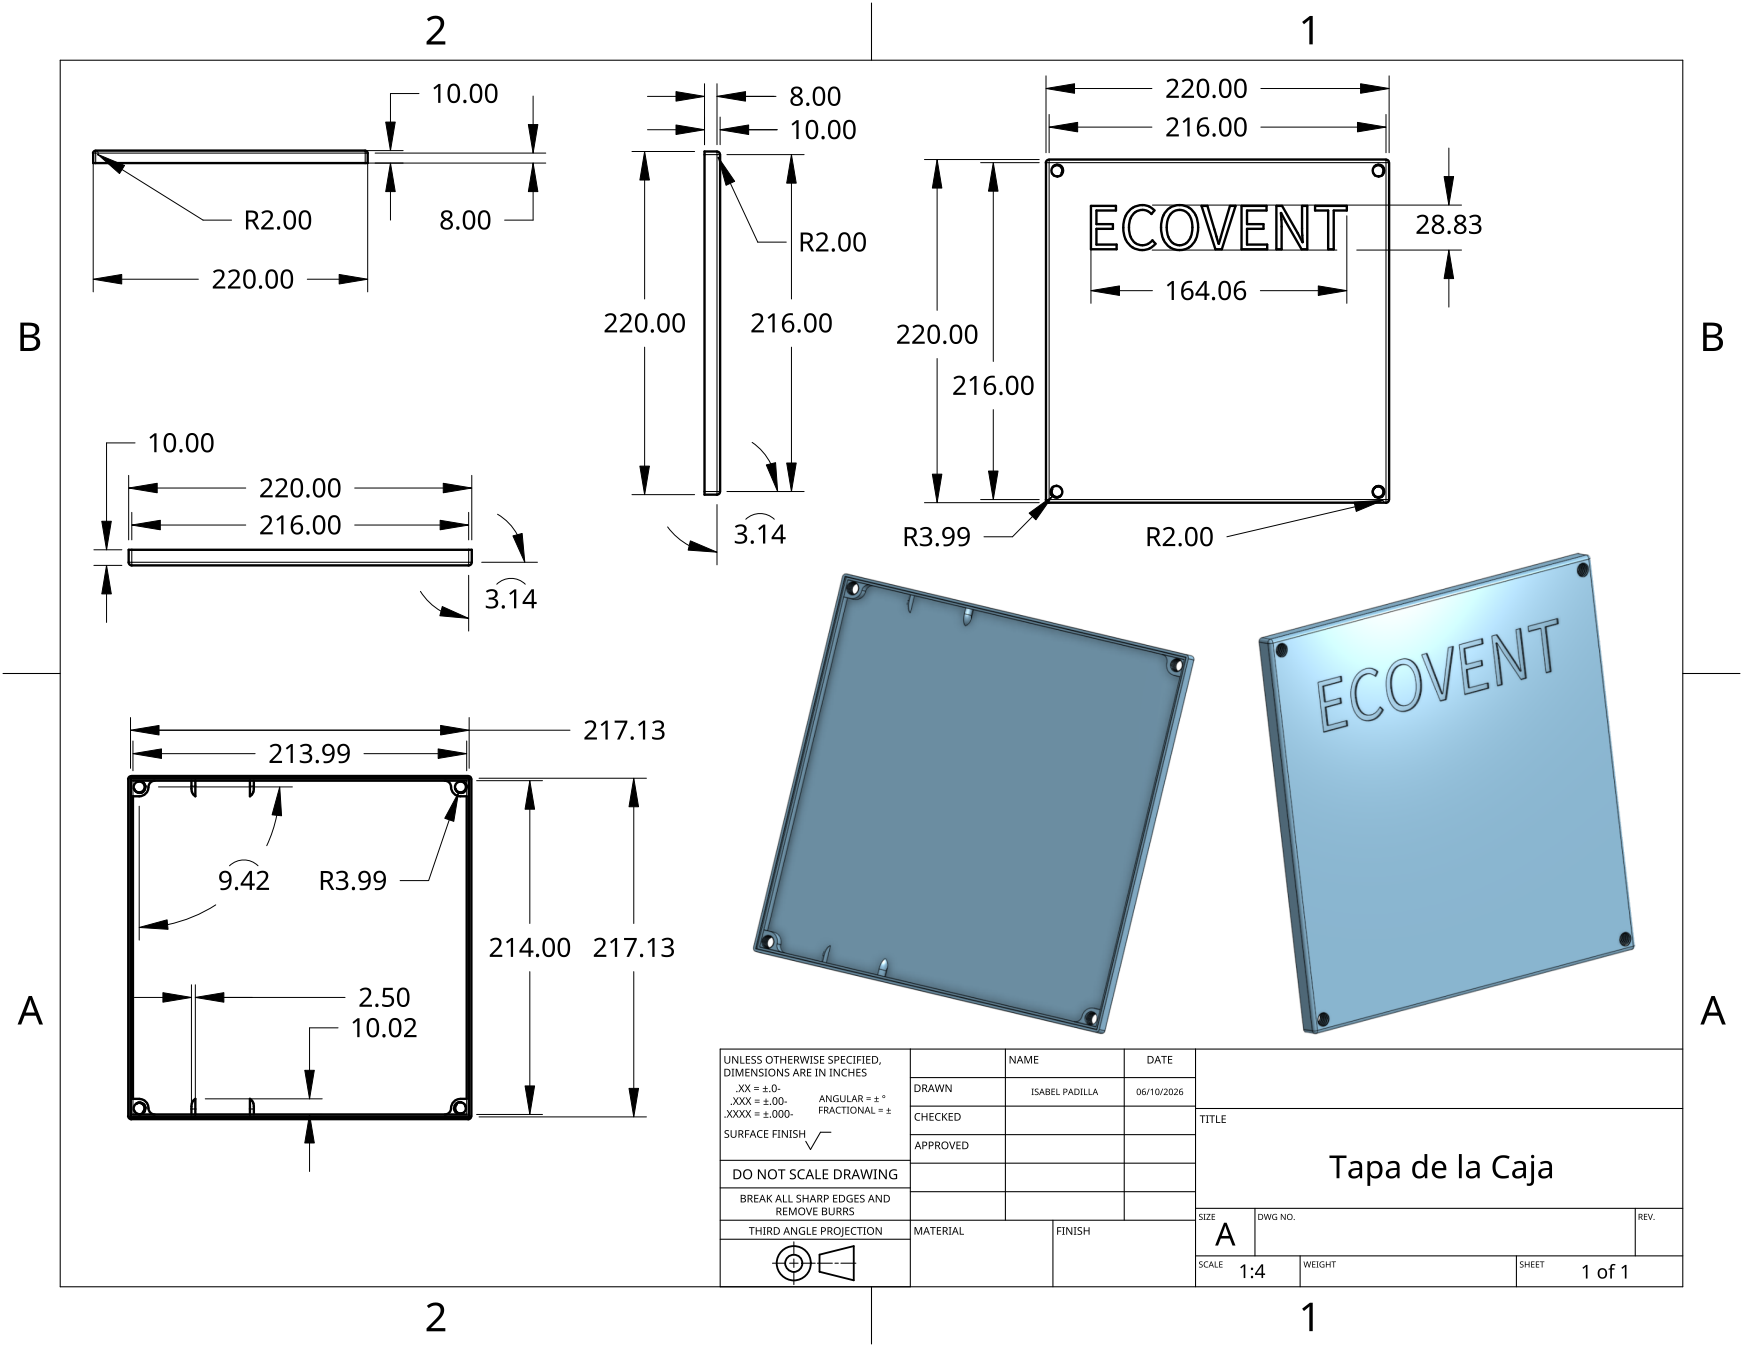
[picture p76: page 1]
