mikepimez/FdD_Equipo_13/Proyecto/MóduloMecánico/VFINAL/Onshape/Planos/ECOVENT Tornillo de la Tapa.pdf

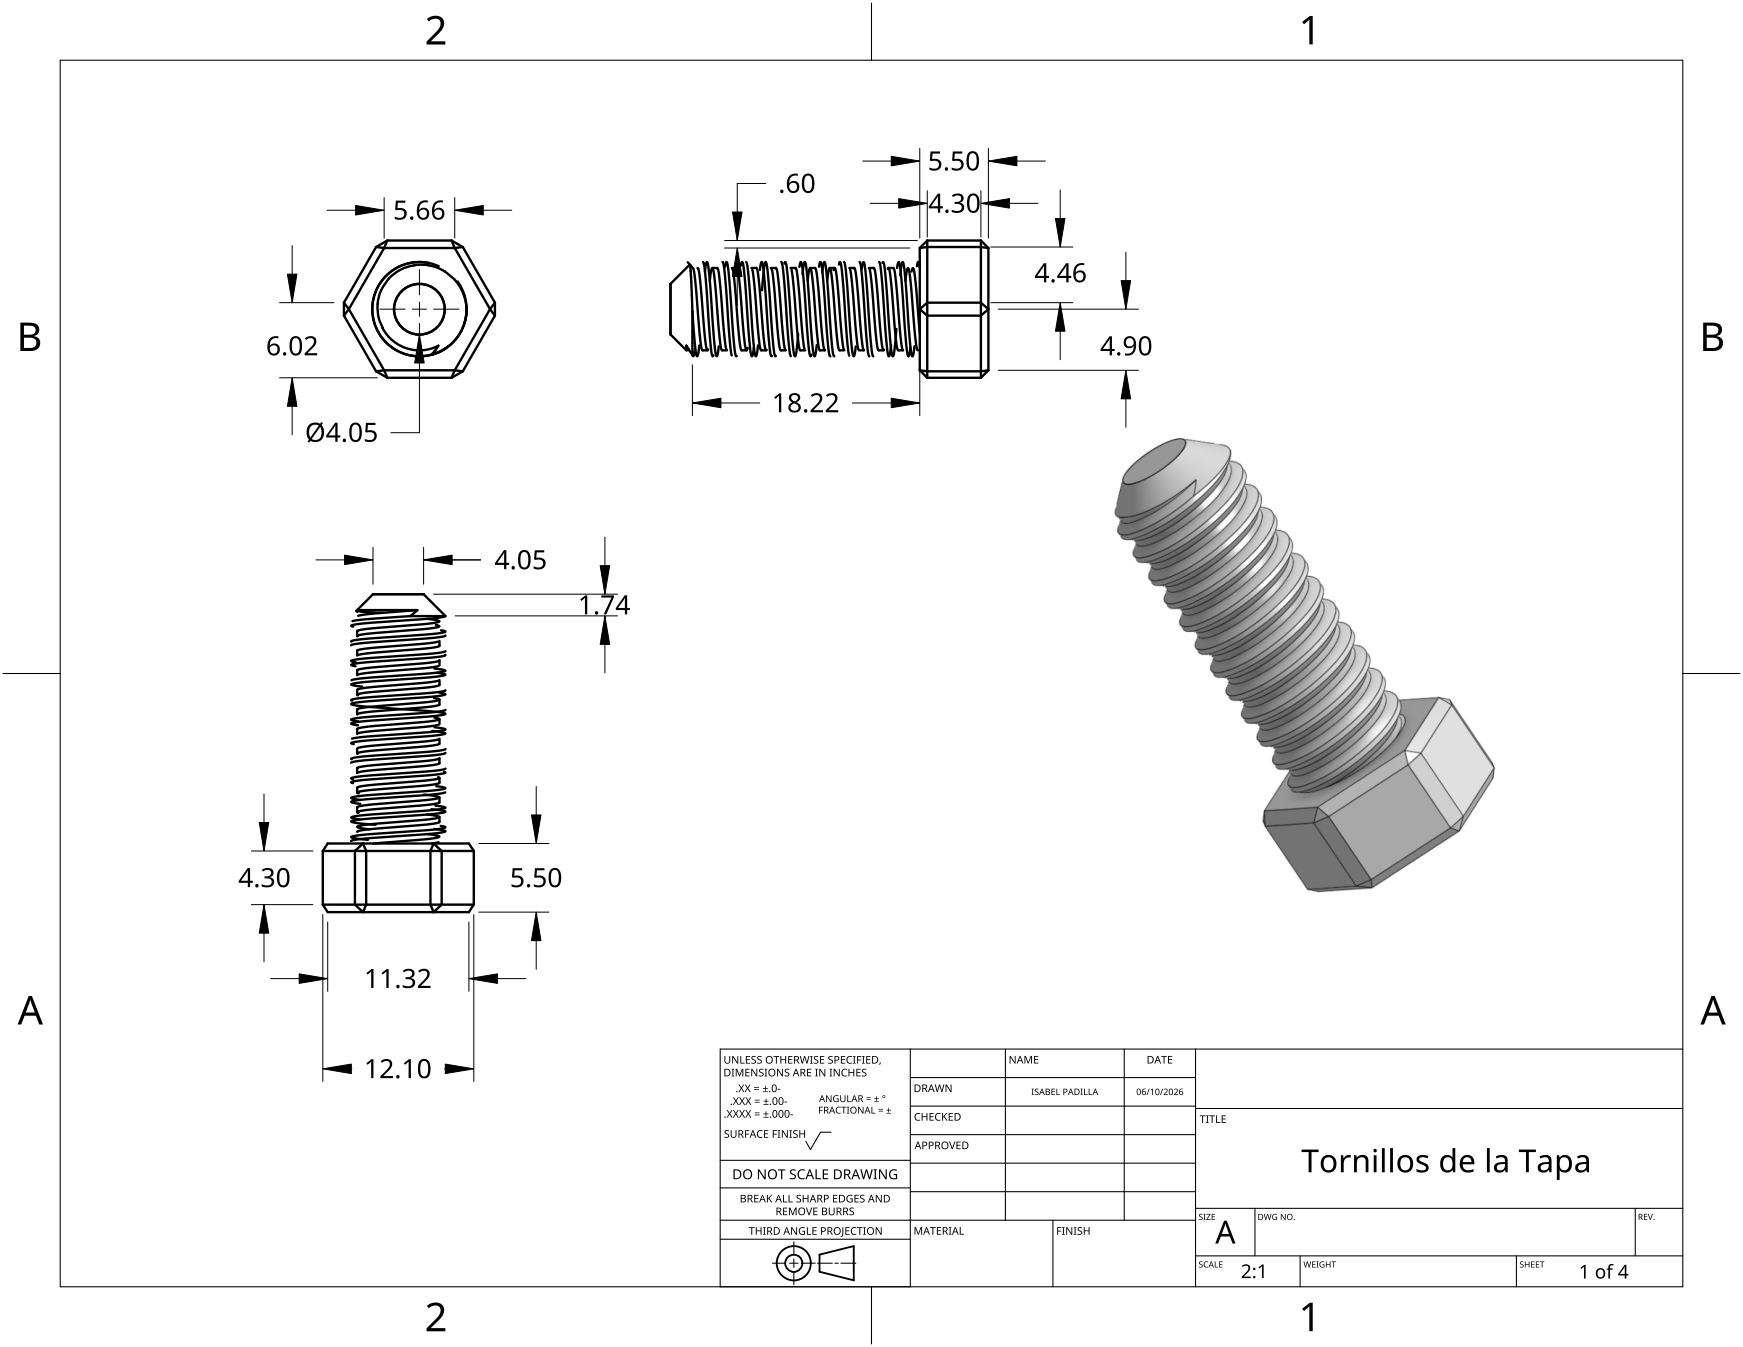
[picture p77: page 1]
