mikepimez/FdD_Equipo_13/Proyecto/MóduloMecánico/VFINAL/Onshape/Planos/ECOVENT Tuerca de Ventiladores.pdf

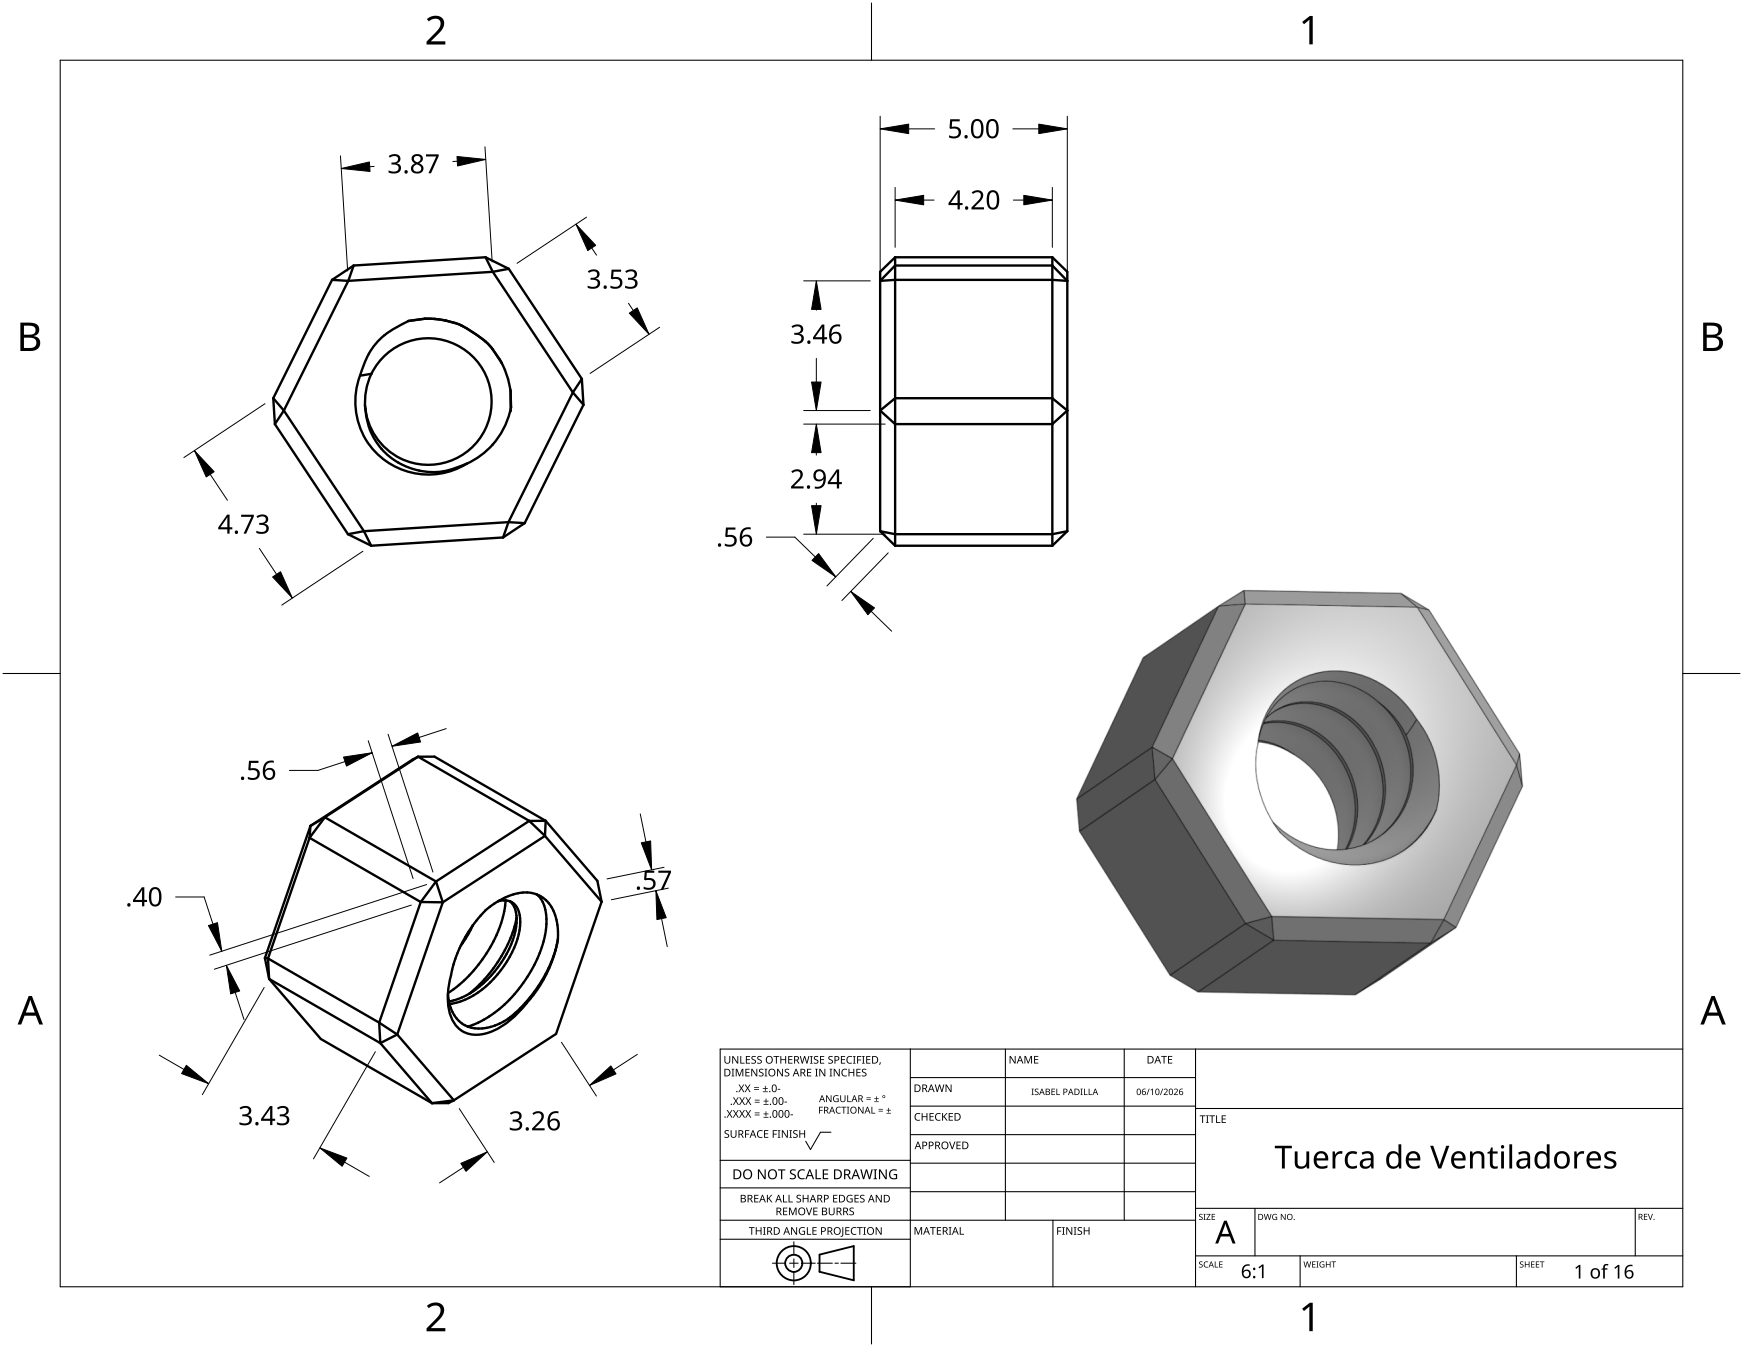
[picture p78: page 1]
