mikepimez/FdD_Equipo_13/Proyecto/MóduloMecánico/V 1.0/Onshape/PLANOS/Tapa.pdf

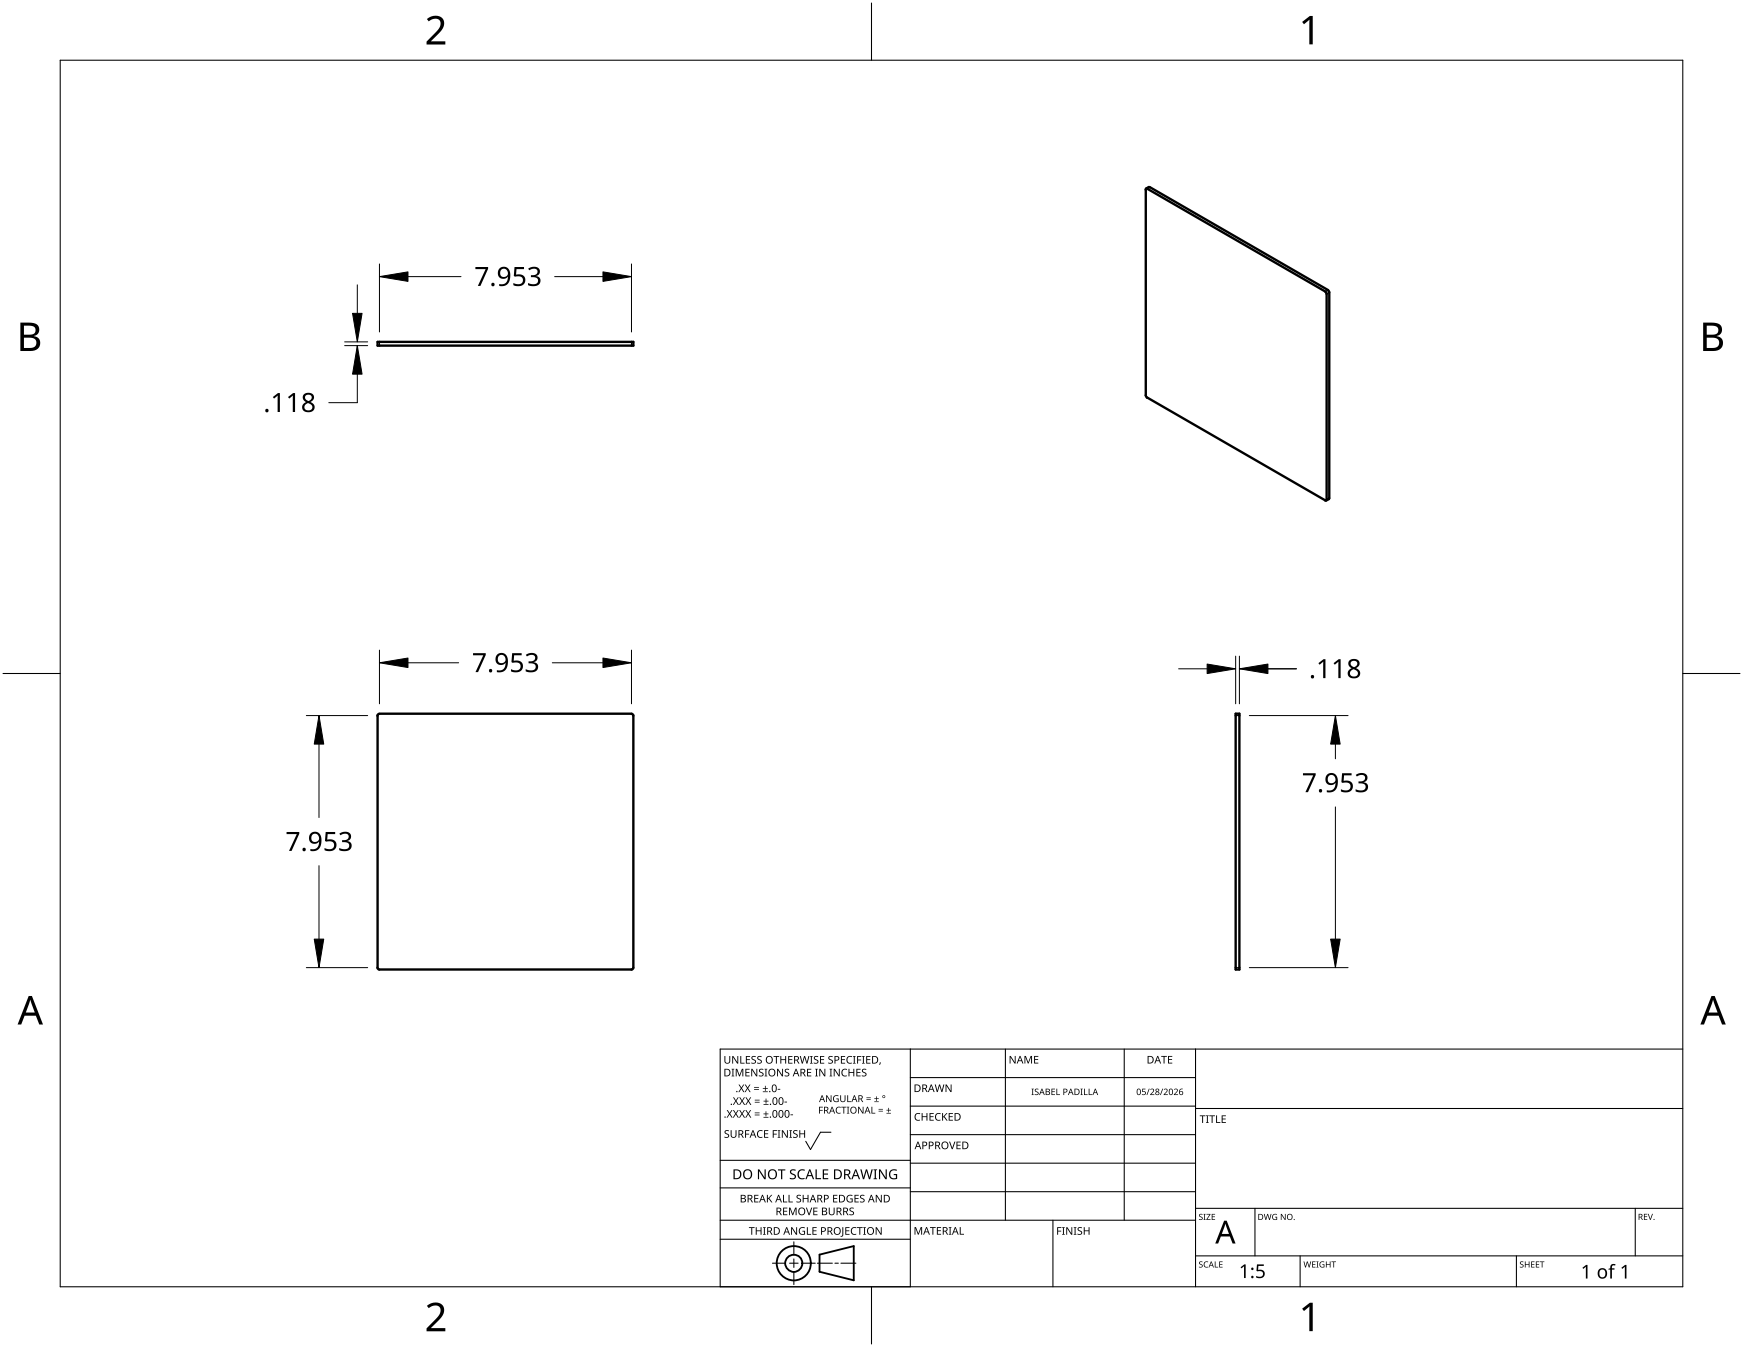
[picture p79: page 1]
