mikepimez/FdD_Equipo_13/Proyecto/MóduloMecánico/V 1.0/Onshape/PLANOS/Parte Inferior.pdf

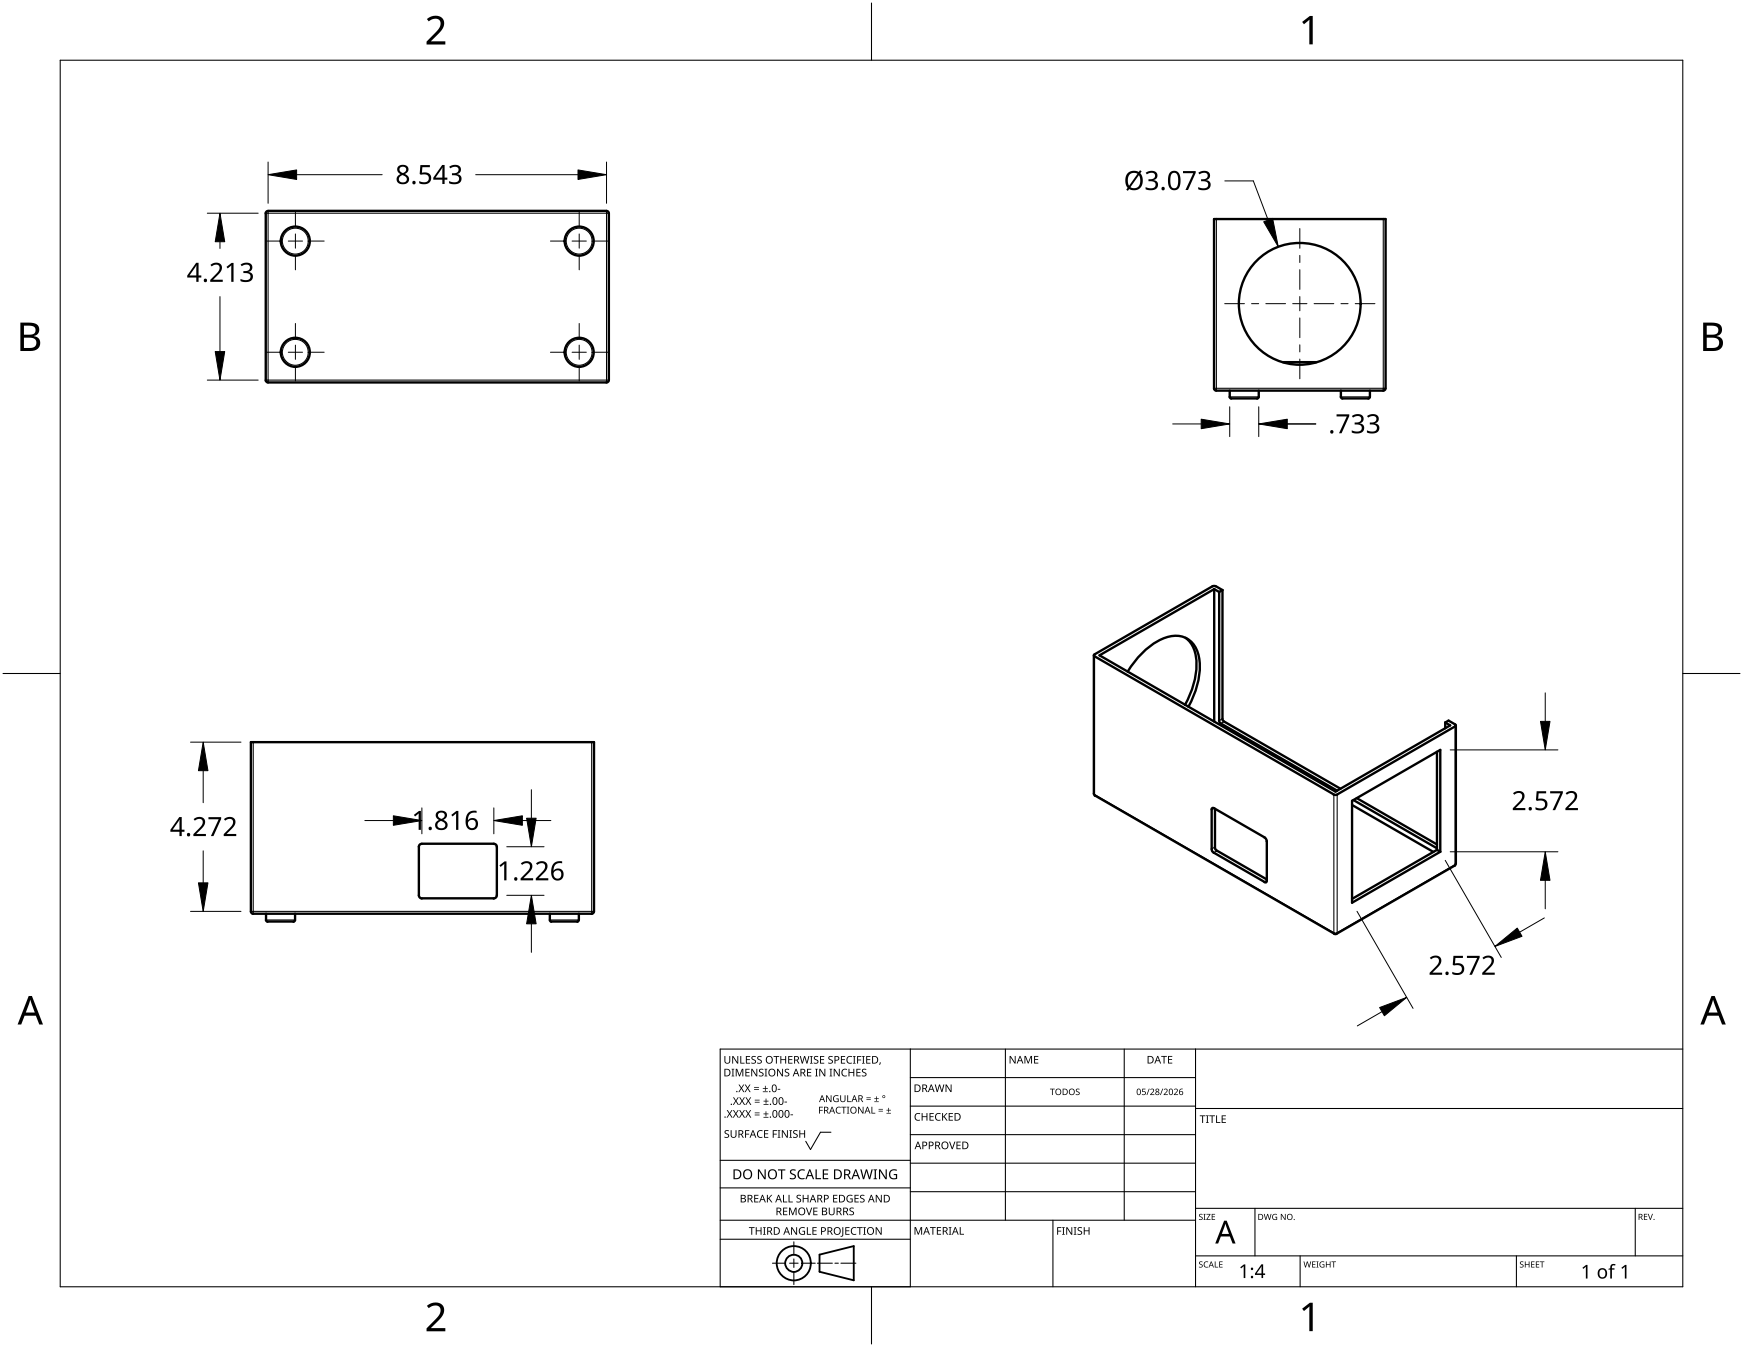
[picture p80: page 1]
