mikepimez/FdD_Equipo_13/Proyecto/MóduloMecánico/V 1.0/Onshape/PLANOS/Parte Superior.pdf

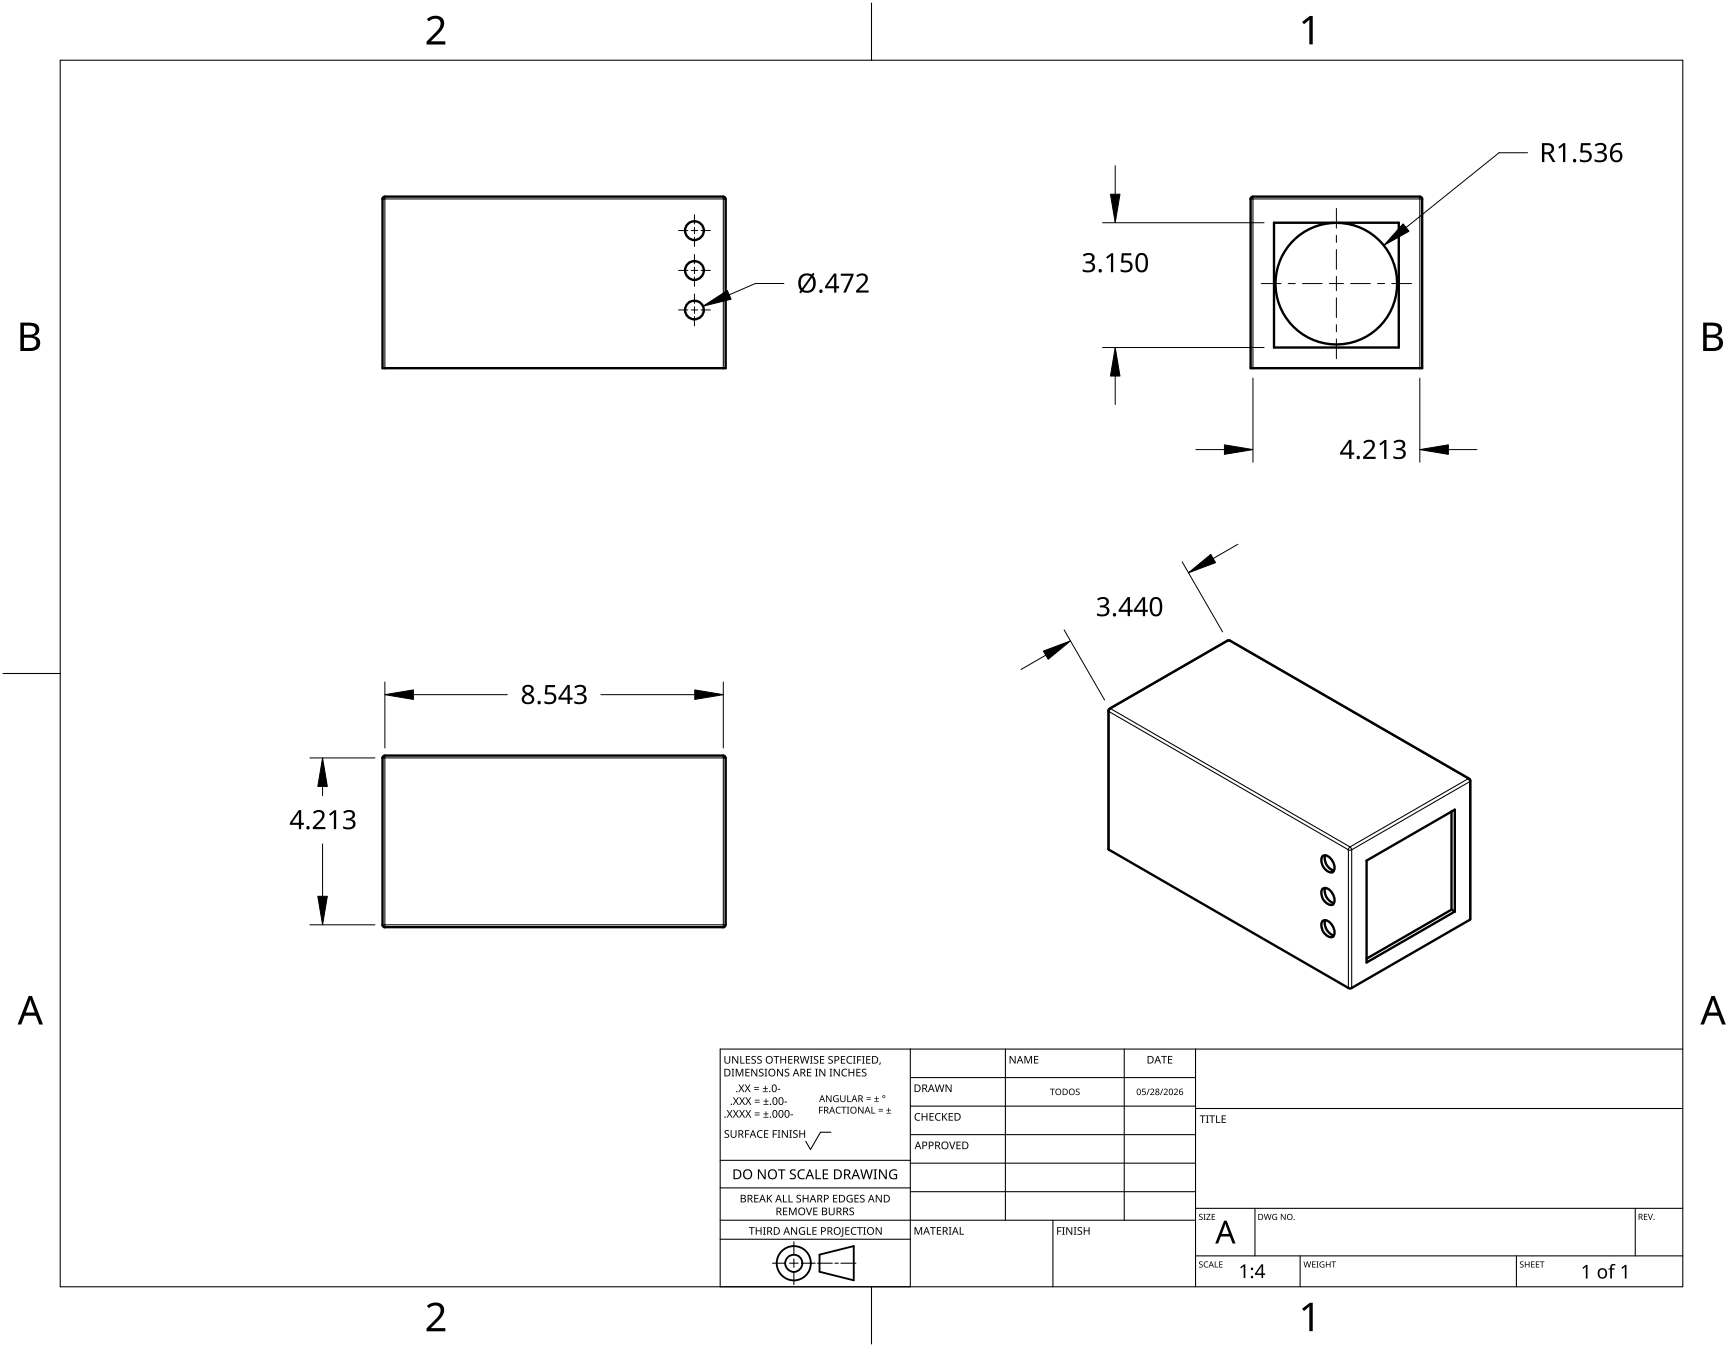
[picture p81: page 1]
